dmkfasi/nus-cpu/kicad/cpu-rcp/PCB-3d-preview-bottom.png

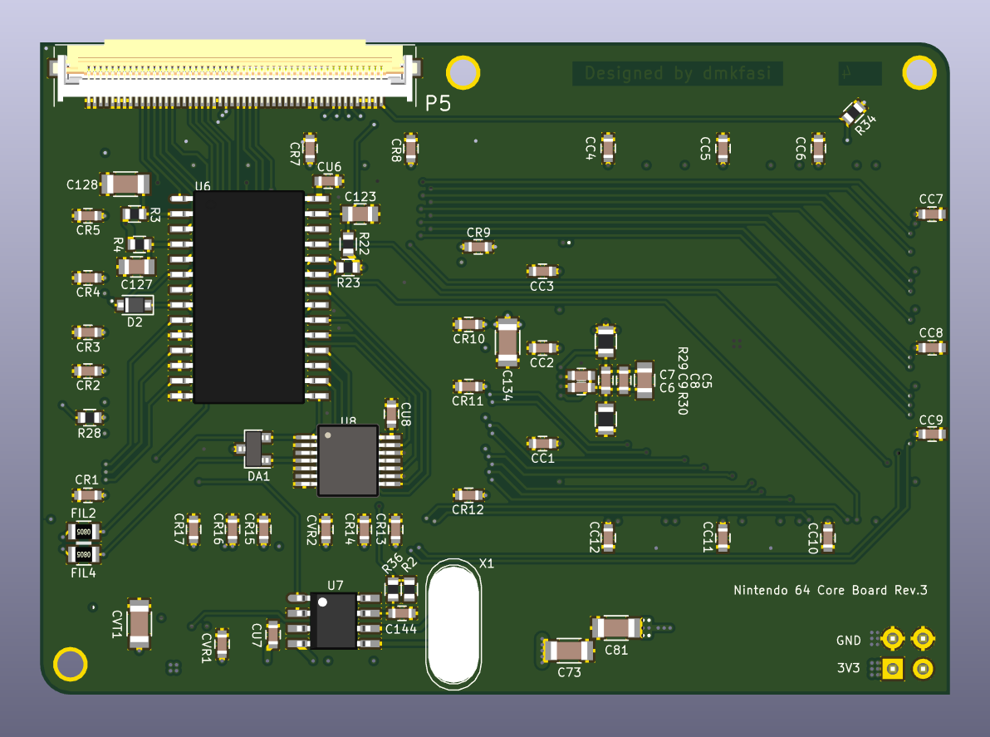
kicad/cpu-rcp/PCB-3d-preview-bottom.png
