dmkfasi/nus-cpu/kicad/cpu-rcp/PCB-3d-preview-top.png

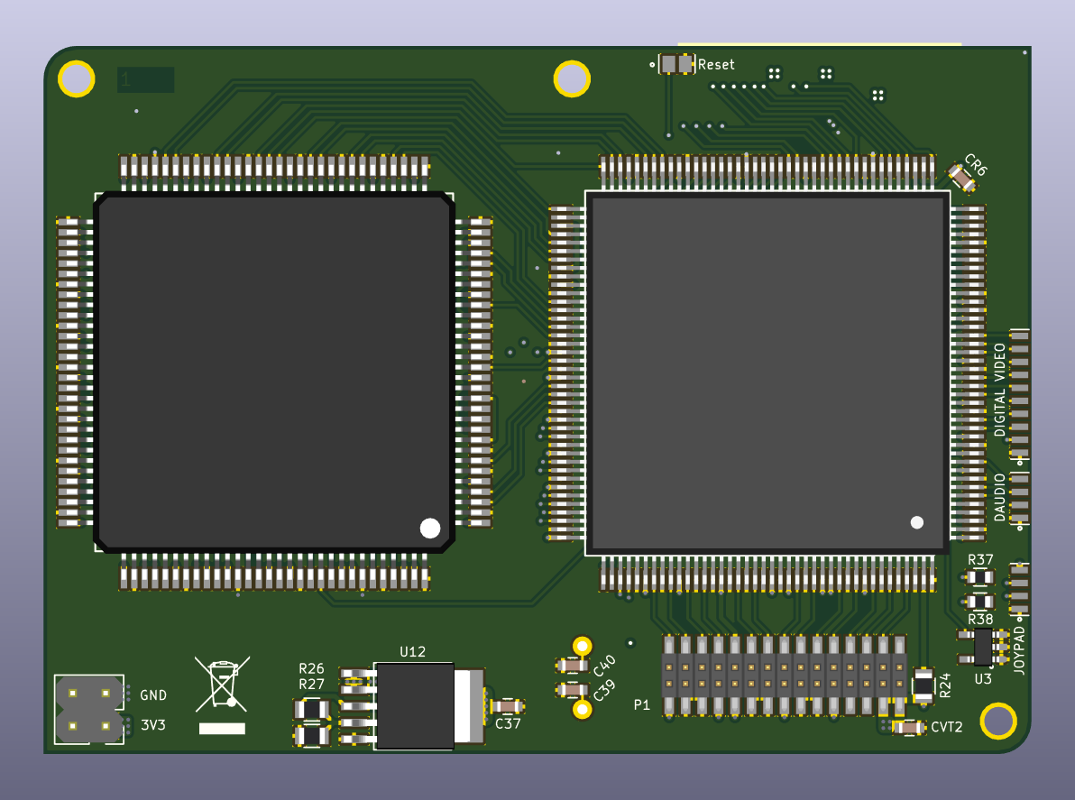
kicad/cpu-rcp/PCB-3d-preview-top.png
