dmkfasi/nus-cpu/kicad/rcp-cart/PCB-3d-preview-bottom.png

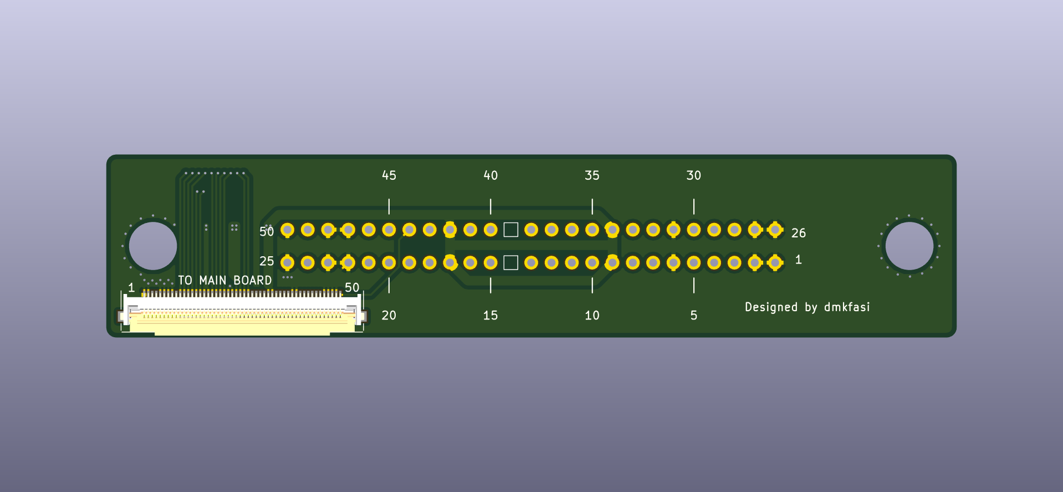
kicad/rcp-cart/PCB-3d-preview-bottom.png
