dmkfasi/nus-cpu/kicad/rcp-cart/PCB-3d-preview-top.png

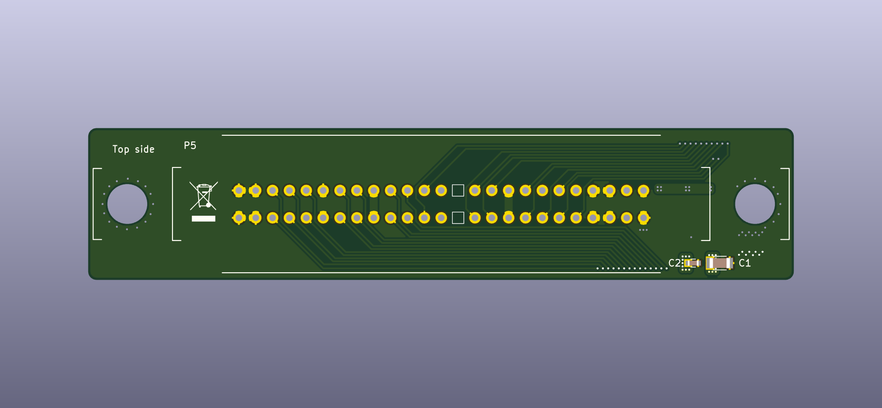
kicad/rcp-cart/PCB-3d-preview-top.png
