dmkfasi/nus-cpu/kicad/rcp-rdram/PCB-3d-preview-bottom.png

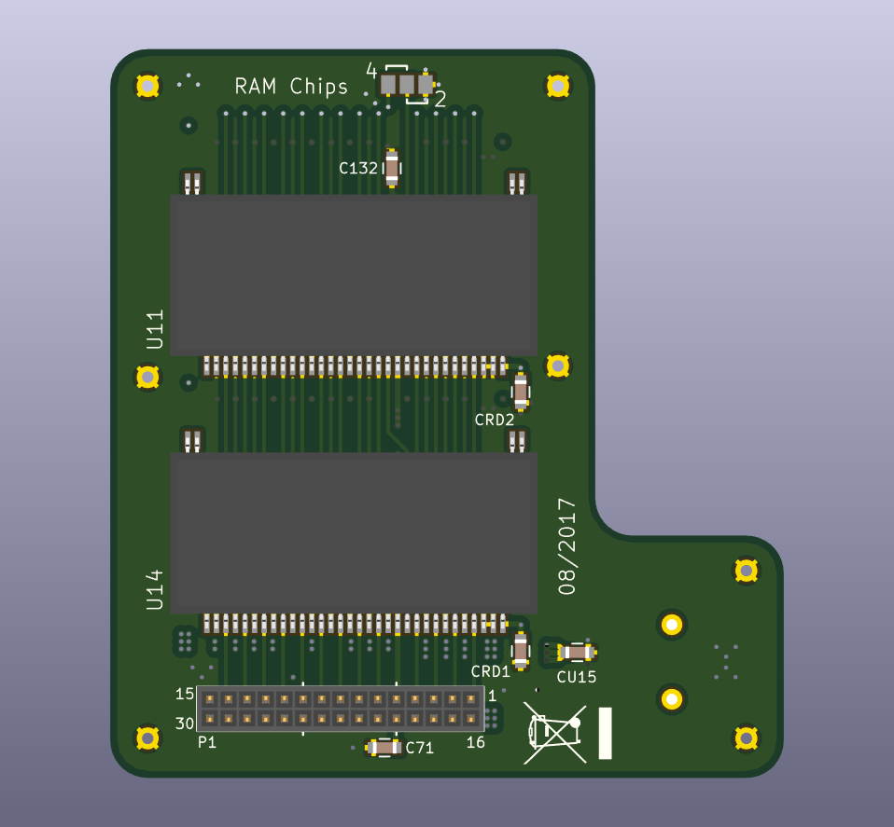
kicad/rcp-rdram/PCB-3d-preview-bottom.png
