dmkfasi/nus-cpu/kicad/rcp-rdram/PCB-3d-preview-top.png

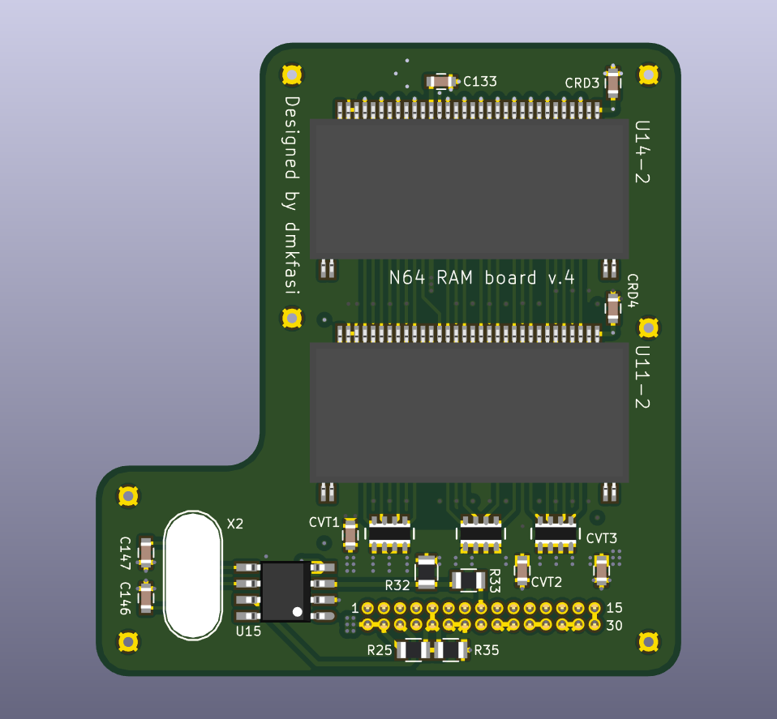
kicad/rcp-rdram/PCB-3d-preview-top.png
