dmkfasi/nus-cpu/reference/n64-marshallh/ra58b10cfc242443986.png

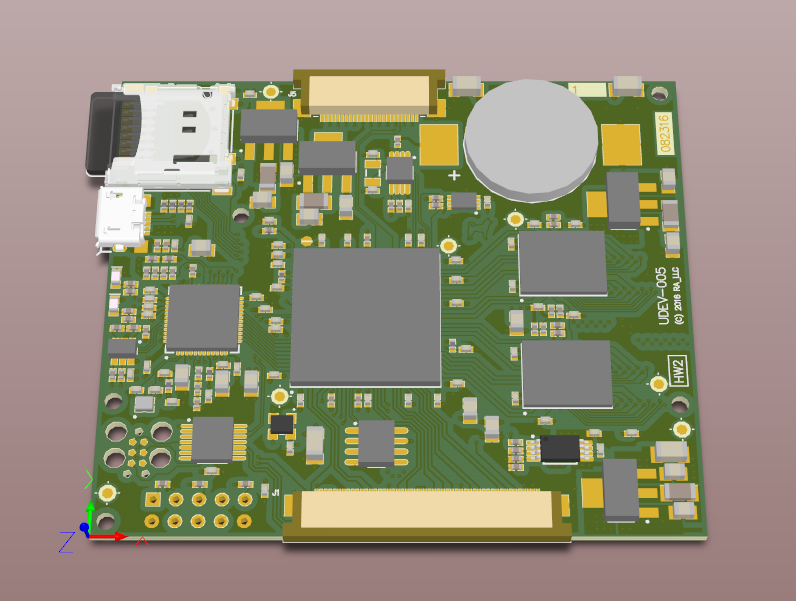
reference/n64-marshallh/ra58b10cfc242443986.png
