dmkfasi/nus-cpu/reference/n64-marshallh/ra58c47a2f7f03d1686.jpg

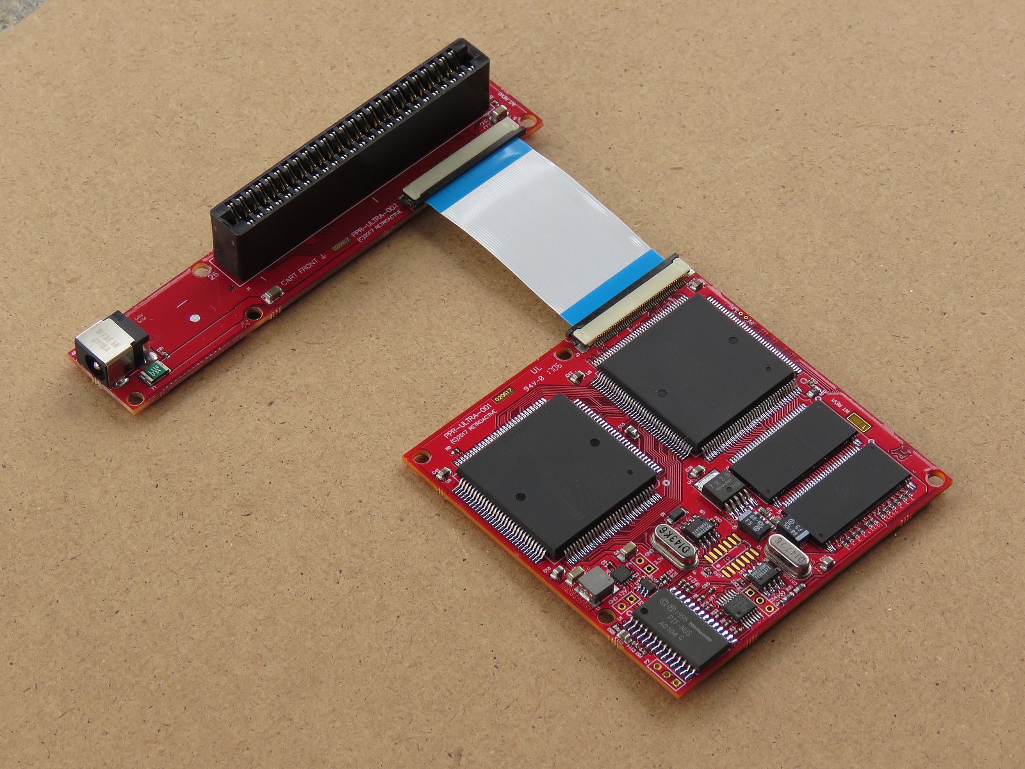
reference/n64-marshallh/ra58c47a2f7f03d1686.jpg
