dmkfasi/nus-cpu/reference/n64-marshallh/ra58c0643a46c8de22f.jpg

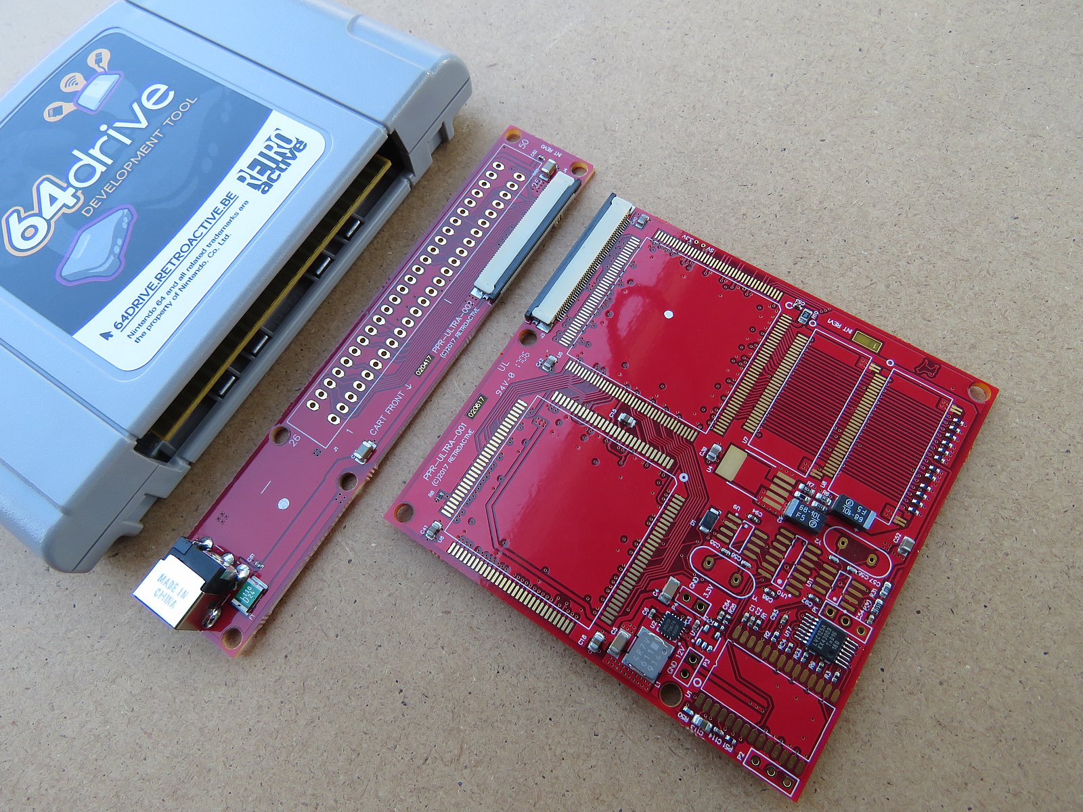
reference/n64-marshallh/ra58c0643a46c8de22f.jpg
