dmkfasi/nus-cpu/reference/n64-marshallh/ra58cd89858b0a0d140.jpg

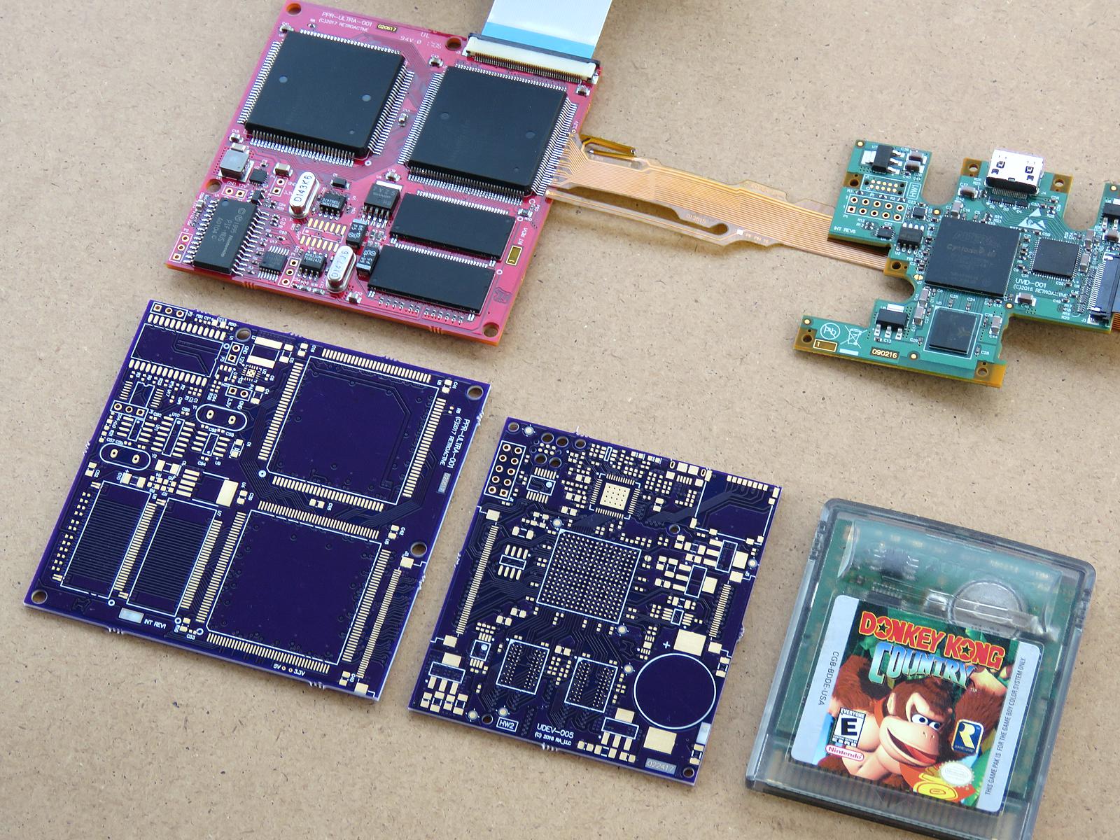
reference/n64-marshallh/ra58cd89858b0a0d140.jpg
