dmkfasi/nus-cpu/reference/n64-marshallh/ra58dc3f5d90e65ff34.jpg

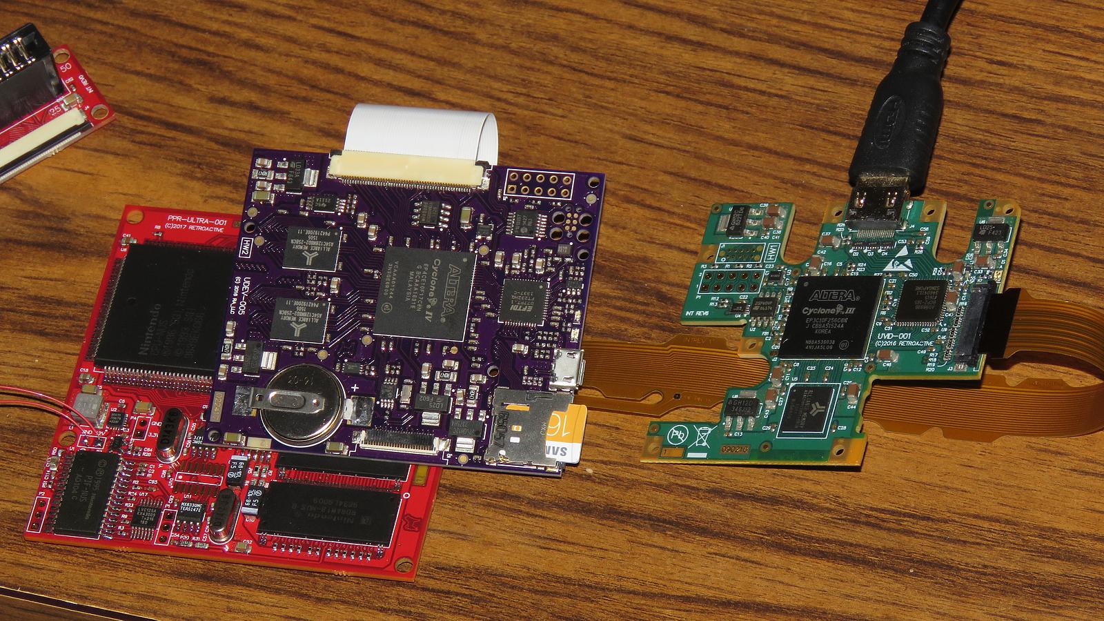
reference/n64-marshallh/ra58dc3f5d90e65ff34.jpg
