dmkfasi/nus-cpu/reference/n64-marshallh/ra58dc427e561e47eda.jpg

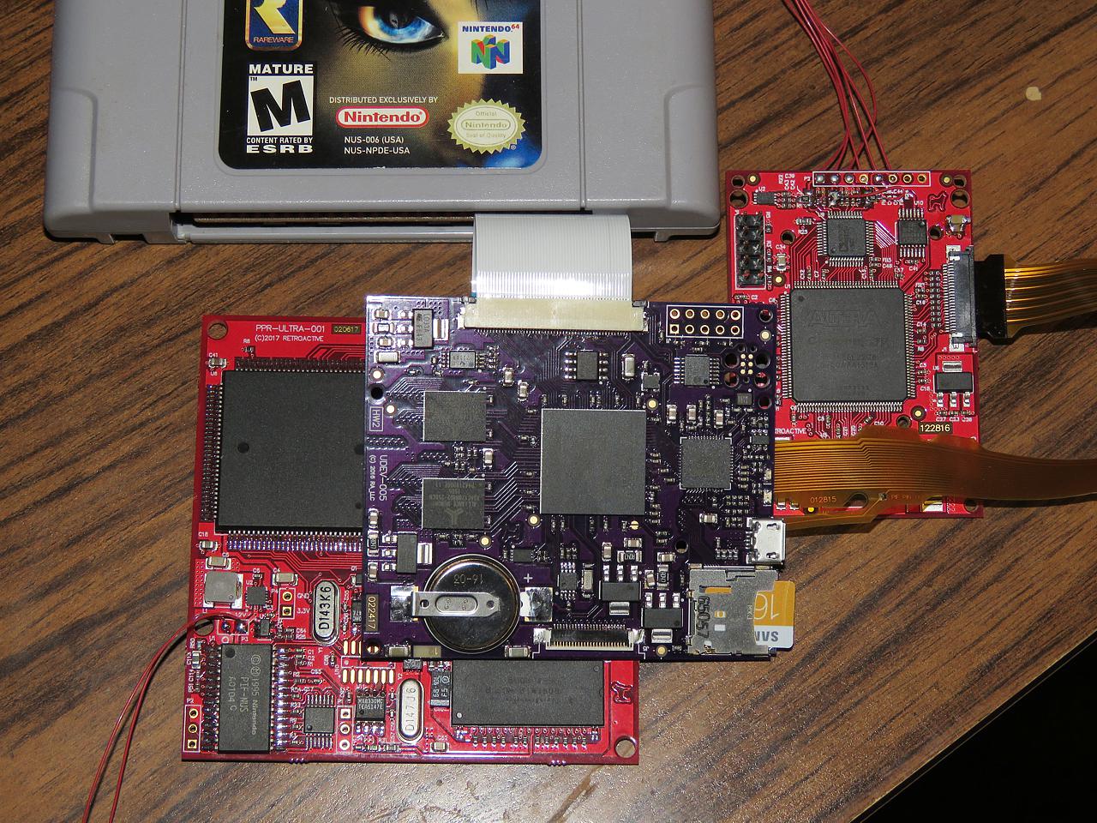
reference/n64-marshallh/ra58dc427e561e47eda.jpg
