dmkfasi/nus-cpu/reference/n64-marshallh/ra58dc394424cff16f6.jpg

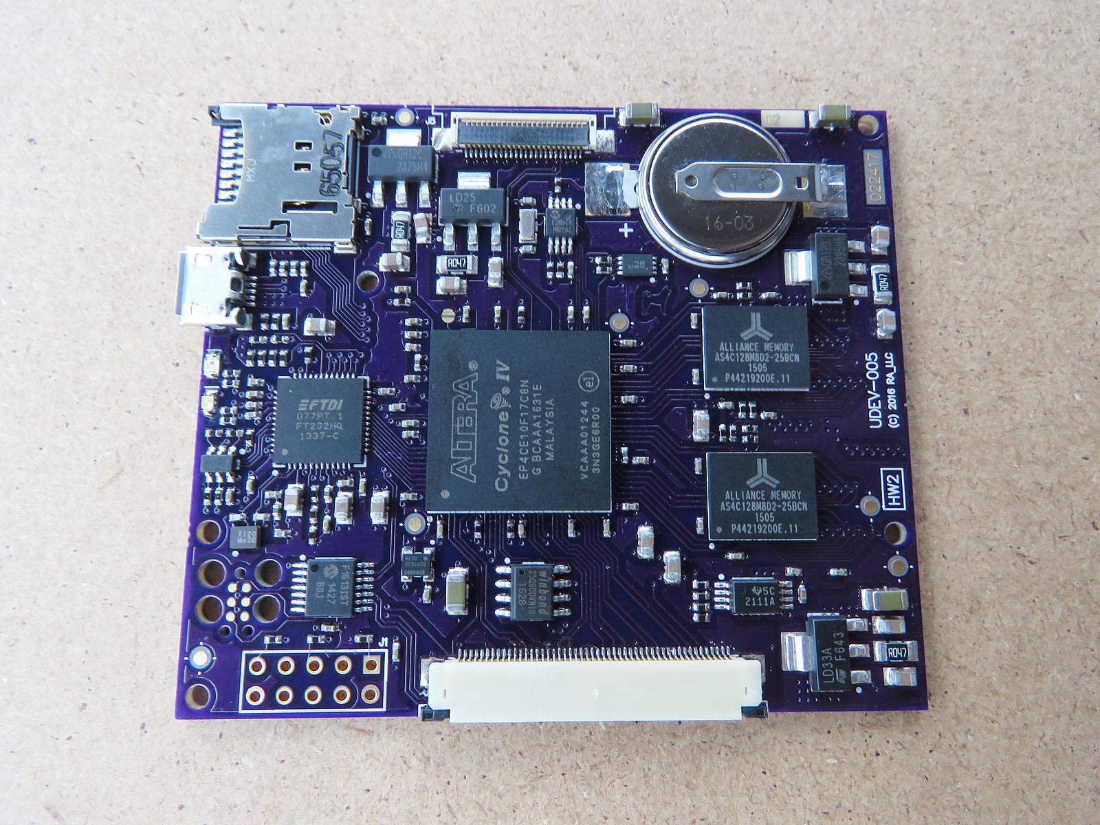
reference/n64-marshallh/ra58dc394424cff16f6.jpg
