dmkfasi/nus-cpu/reference/n64-marshallh/ra58fe89d2181fc5a18.png

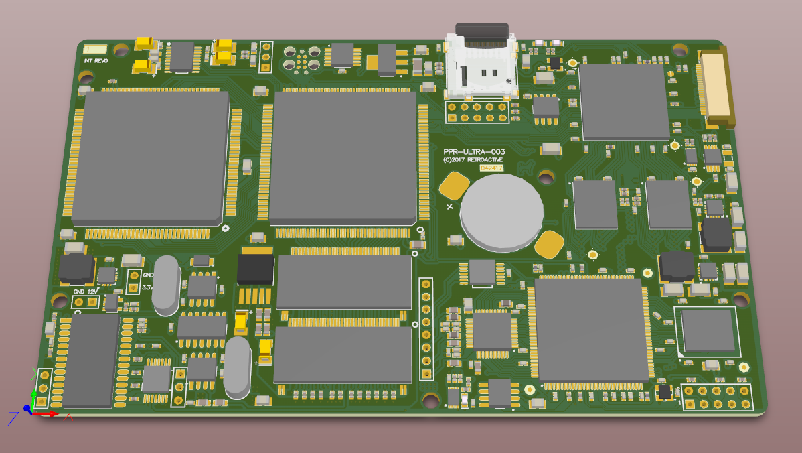
reference/n64-marshallh/ra58fe89d2181fc5a18.png
