dmkfasi/nus-cpu/reference/n64-marshallh/ra58fe877286c67c202.png

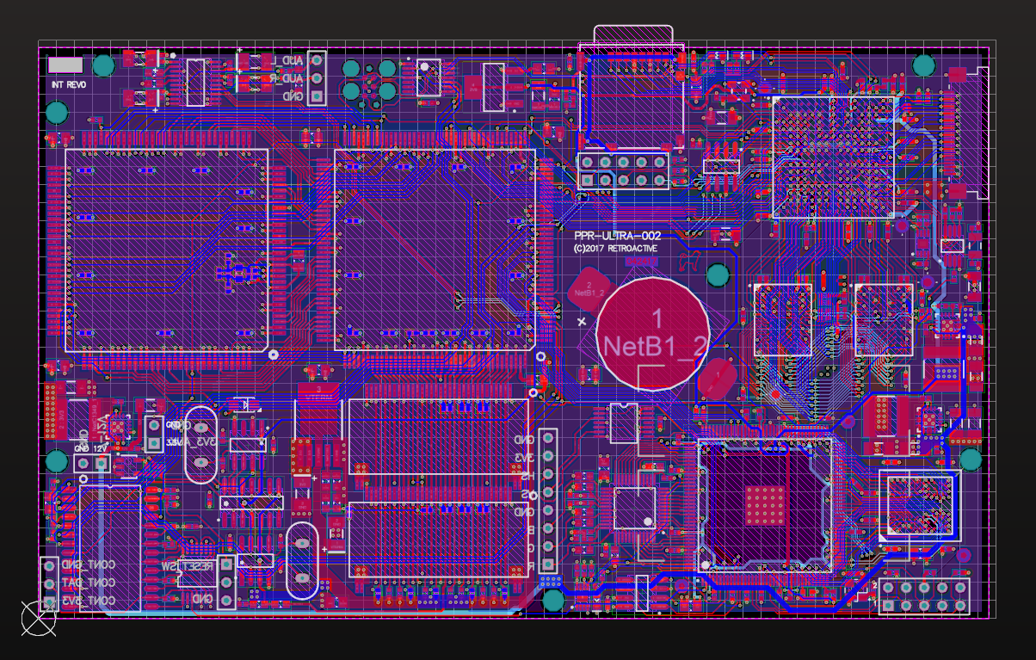
reference/n64-marshallh/ra58fe877286c67c202.png
