dmkfasi/nus-cpu/reference/n64-marshallh/ra588ce74976bb9afa8.jpg

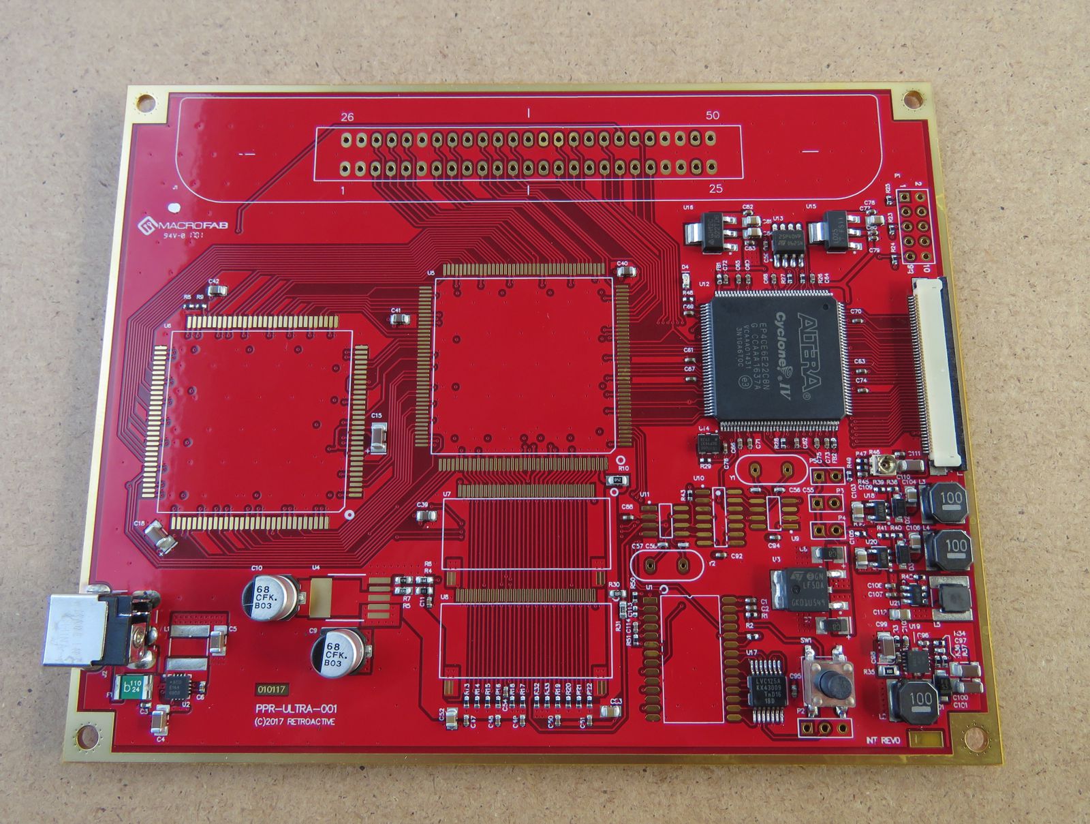
reference/n64-marshallh/ra588ce74976bb9afa8.jpg
