dmkfasi/nus-cpu/reference/n64-marshallh/ra588e489f1ec7b8442.jpg

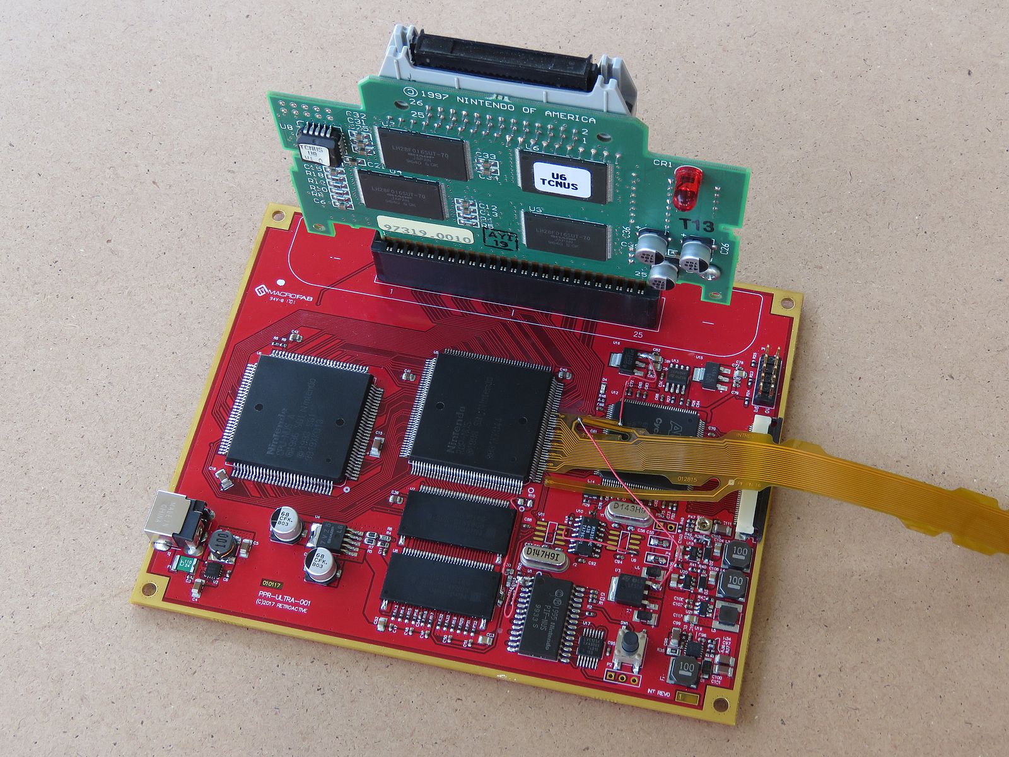
reference/n64-marshallh/ra588e489f1ec7b8442.jpg
