dmkfasi/nus-cpu/reference/n64-marshallh/ra5869ab79de0d7c09b.png

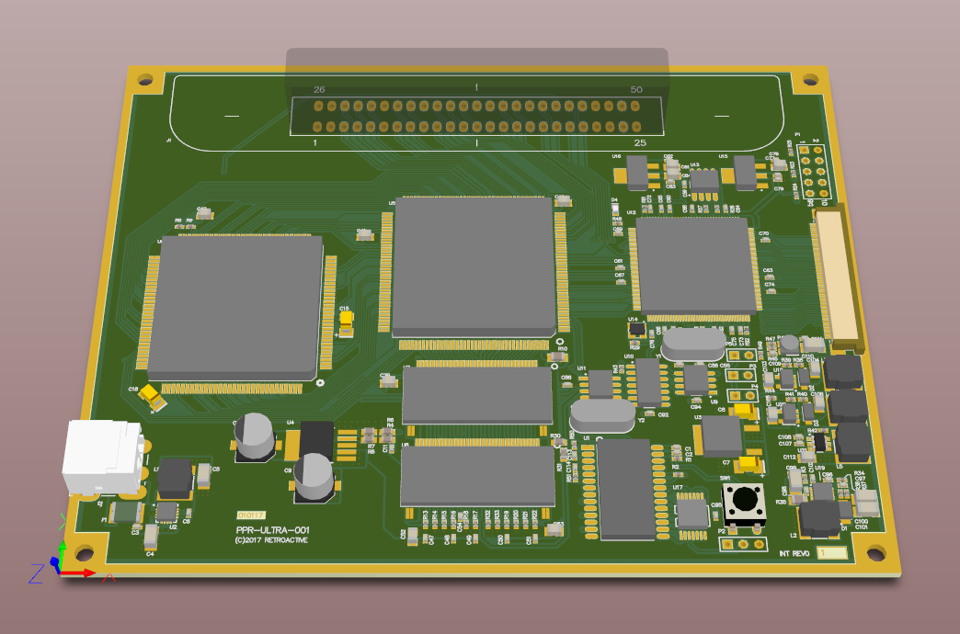
reference/n64-marshallh/ra5869ab79de0d7c09b.png
