dmkfasi/nus-cpu/reference/n64-marshallh/ra5869d1bb45a788b08.png

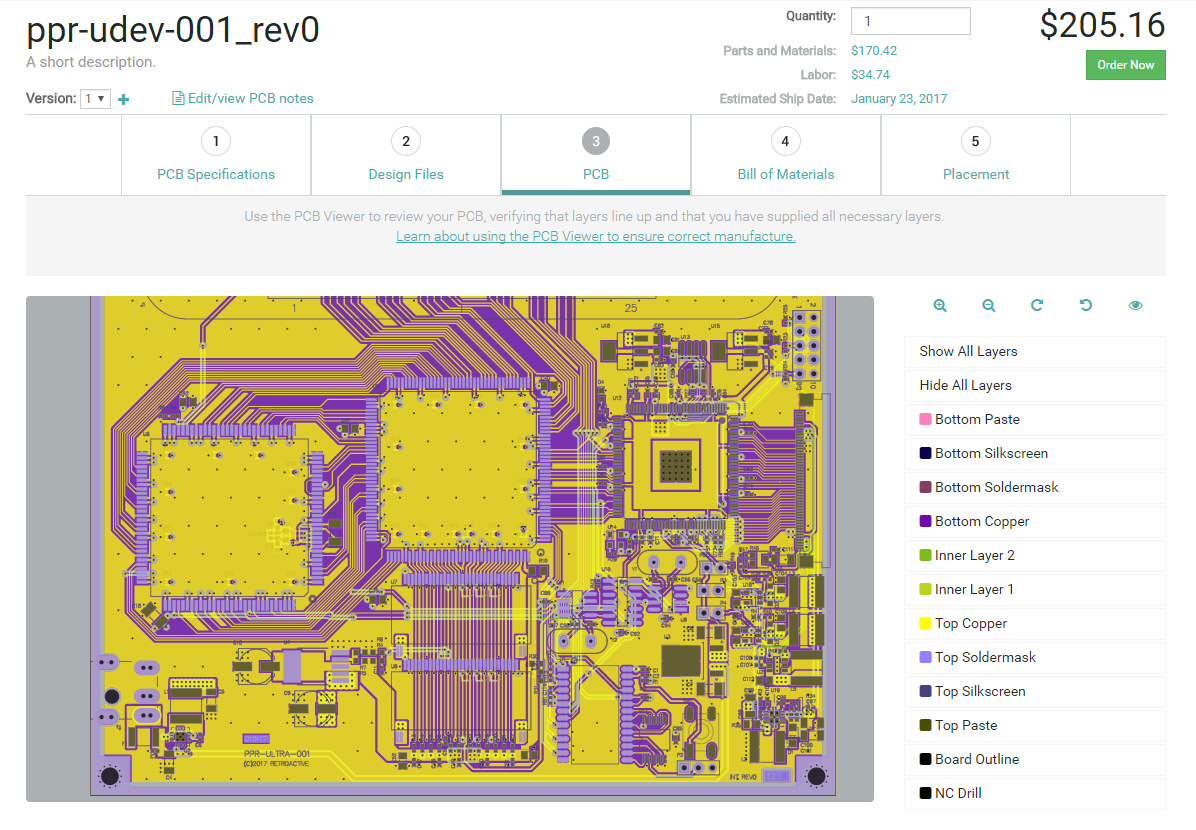
reference/n64-marshallh/ra5869d1bb45a788b08.png
