dmkfasi/nus-cpu/reference/n64-marshallh/ra5877c3ecaf056e521.png

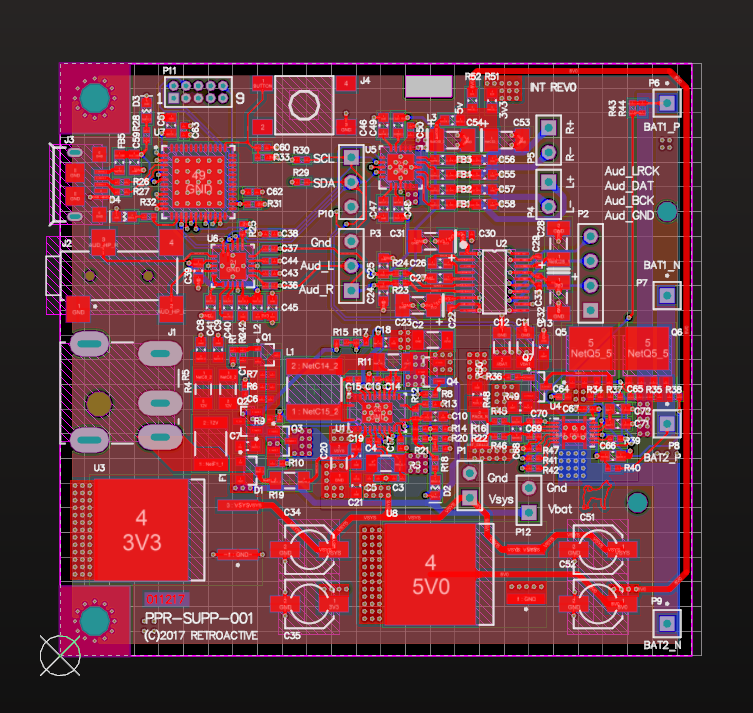
reference/n64-marshallh/ra5877c3ecaf056e521.png
