dmkfasi/nus-cpu/reference/n64-marshallh/ra5877c6db6ab1510e0.png

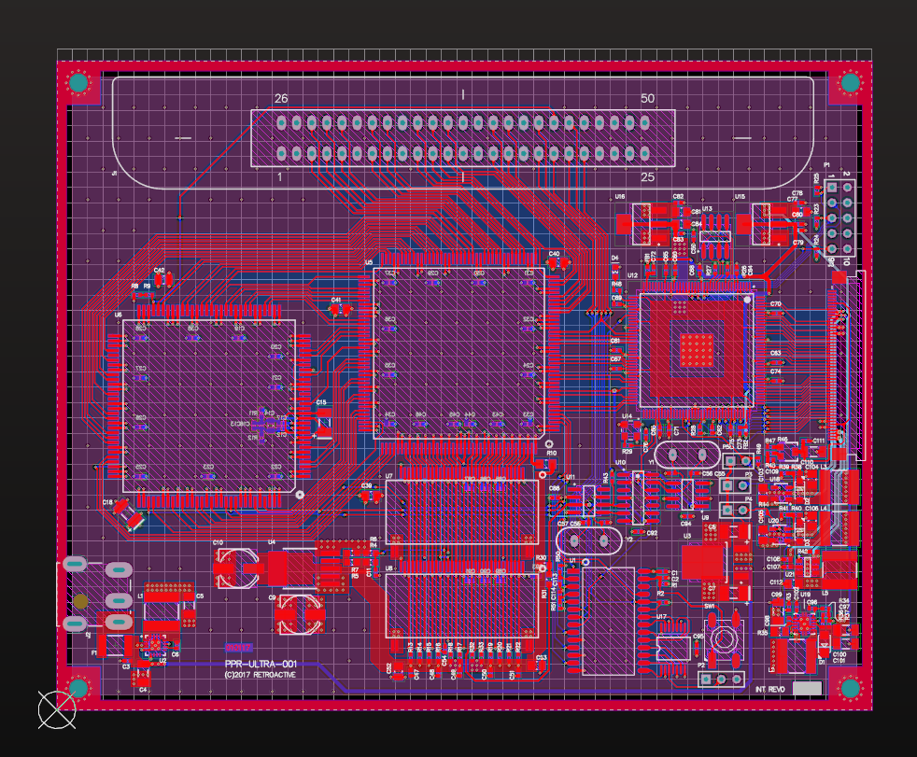
reference/n64-marshallh/ra5877c6db6ab1510e0.png
