dmkfasi/nus-cpu/reference/n64-marshallh/ra5925fa05948f99520.jpg

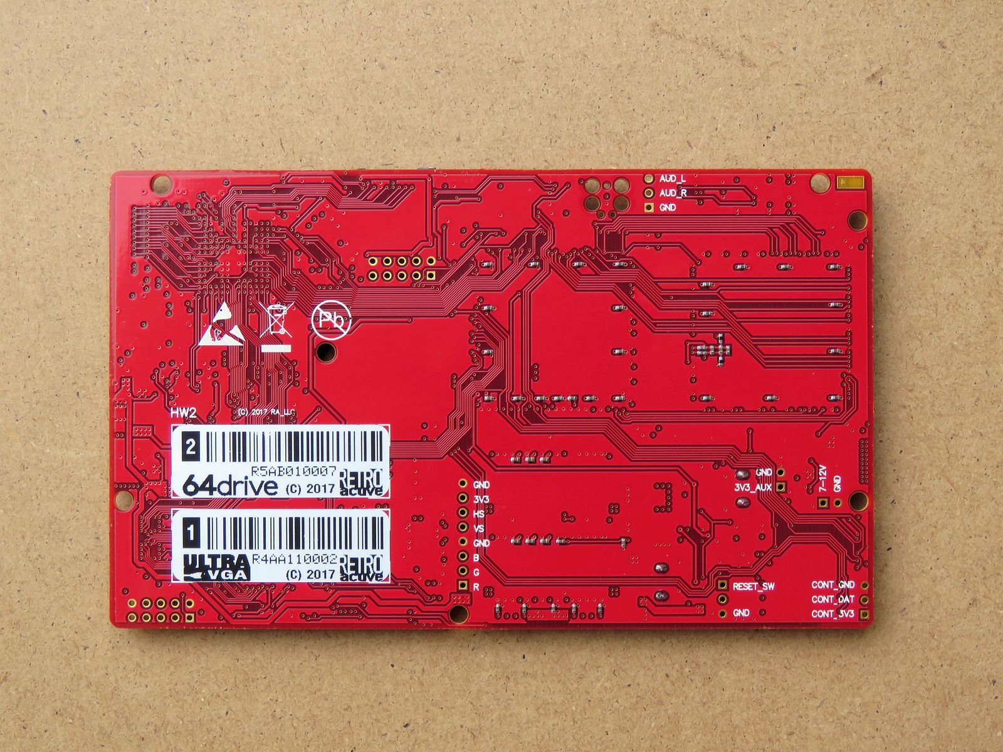
reference/n64-marshallh/ra5925fa05948f99520.jpg
