dmkfasi/nus-cpu/reference/n64-marshallh/ra5925fc53f3825d982.jpg

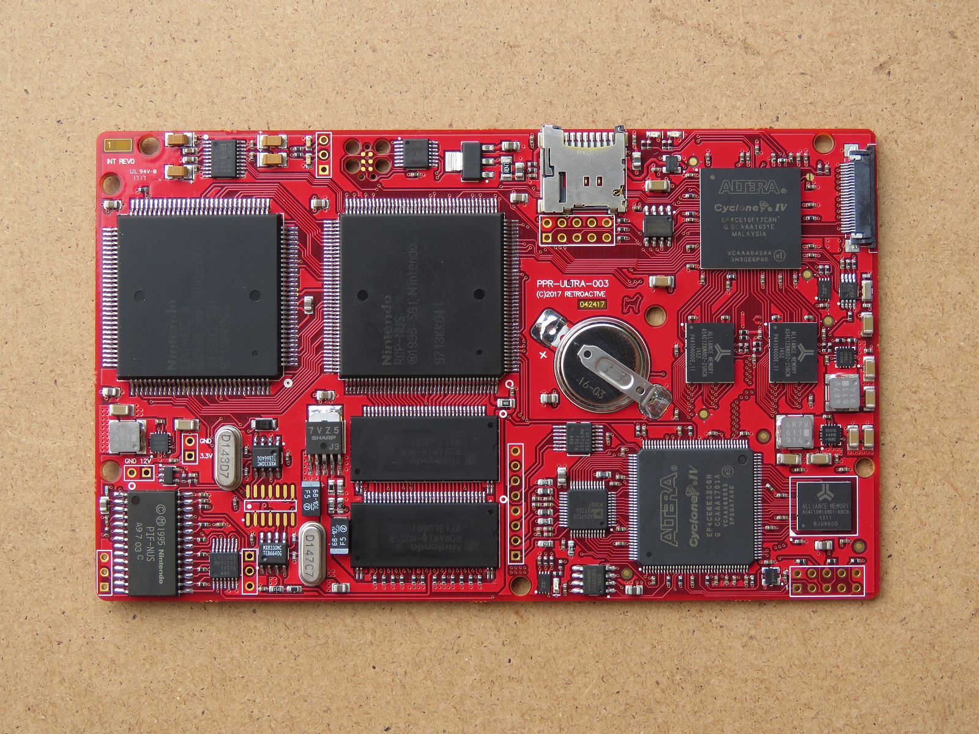
reference/n64-marshallh/ra5925fc53f3825d982.jpg
