dmkfasi/nus-cpu/reference/n64-marshallh/ra5959c7e0f3a951d8c.jpg

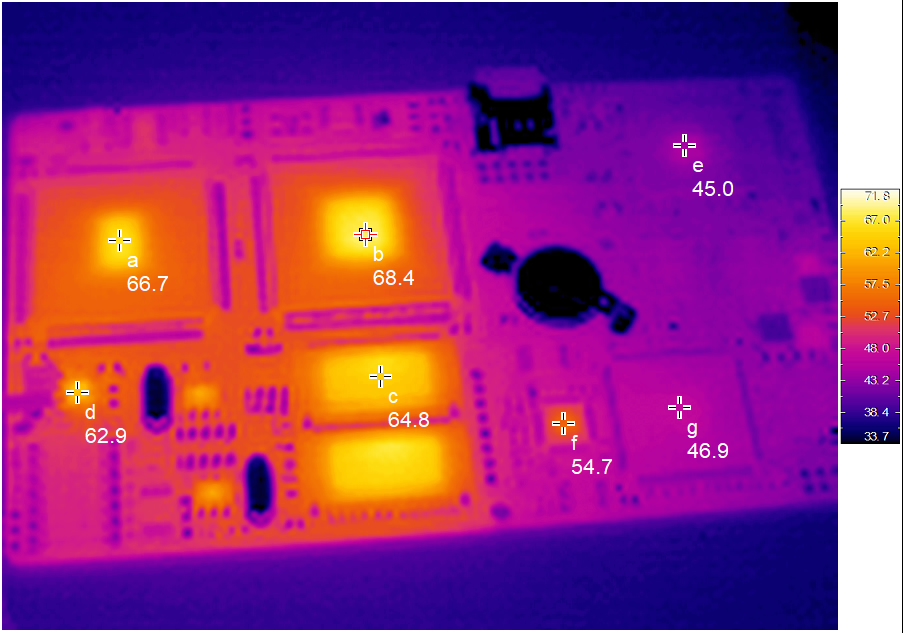
reference/n64-marshallh/ra5959c7e0f3a951d8c.jpg
