dmkfasi/nus-cpu/reference/n64-marshallh/ra58771da7159c2eef9.png

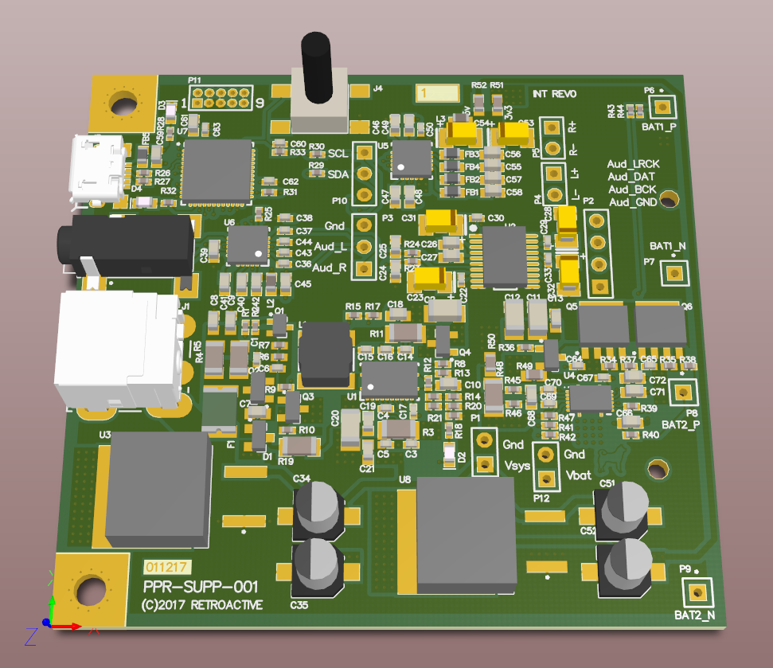
reference/n64-marshallh/ra58771da7159c2eef9.png
