dmkfasi/nus-cpu/reference/n64-marshallh/ra58929f7f12cb957d5.jpg

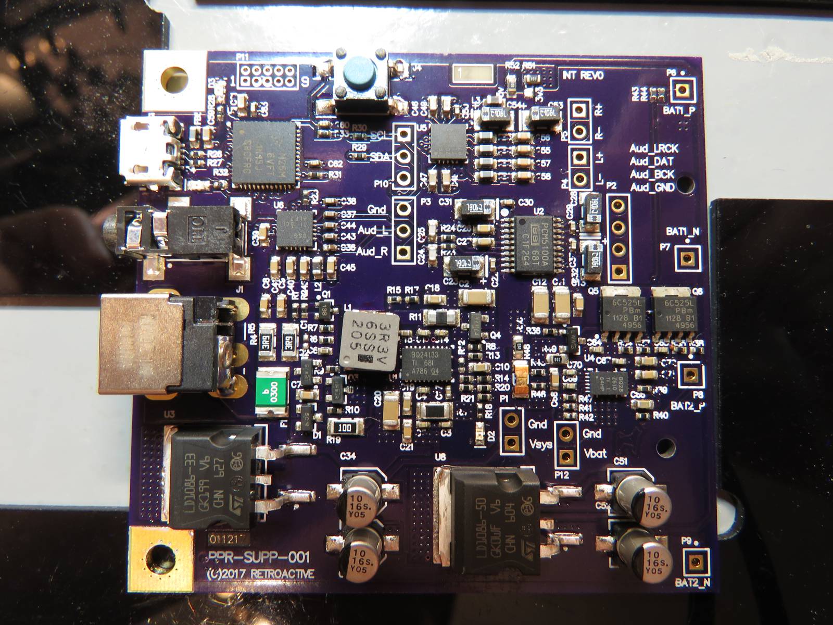
reference/n64-marshallh/ra58929f7f12cb957d5.jpg
