dmkfasi/nus-cpu/reference/n64-marshallh/ra59654d515e9111a43.jpg

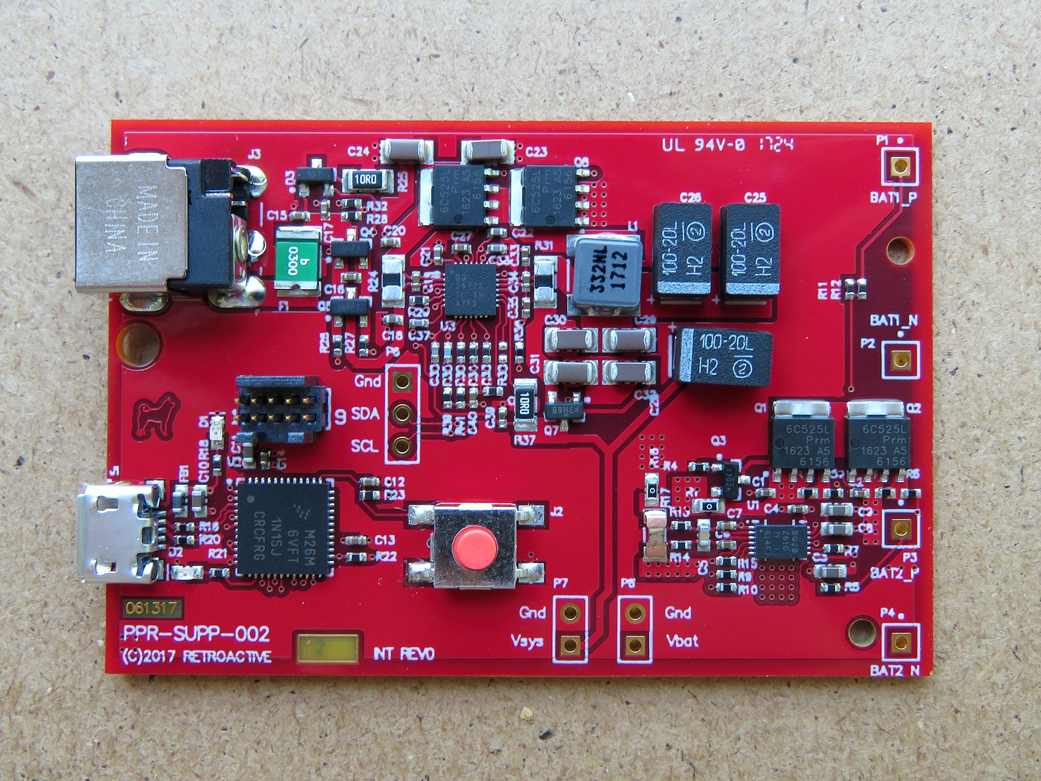
reference/n64-marshallh/ra59654d515e9111a43.jpg
