dmkfasi/nus-cpu/reference/n64-marshallh/ra586701c5acb63817e.png

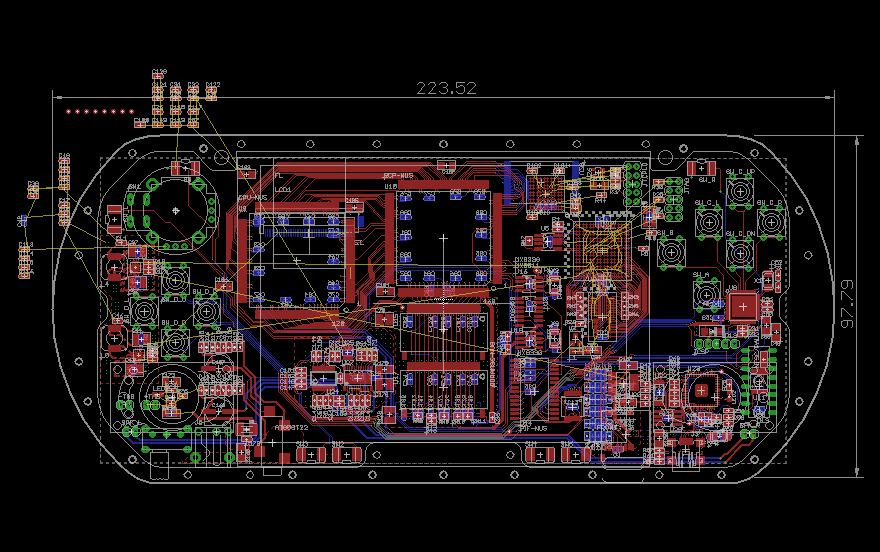
reference/n64-marshallh/ra586701c5acb63817e.png
