dmkfasi/nus-cpu/reference/n64-marshallh/ra586845e5d66768dc4.png

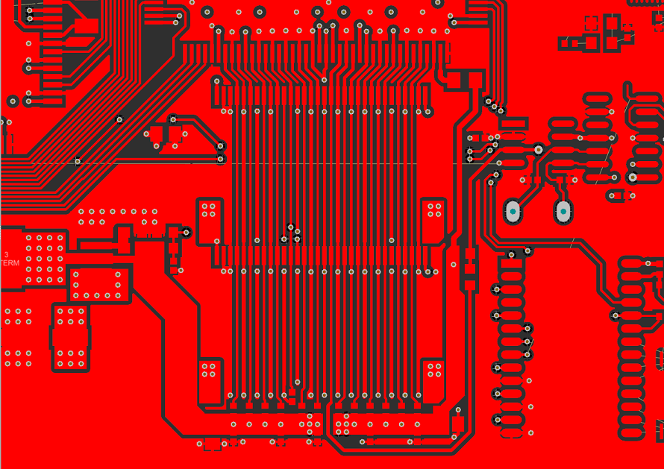
reference/n64-marshallh/ra586845e5d66768dc4.png
