dmkfasi/nus-cpu/reference/n64-marshallh/ra5886822dd67f325fe.jpg

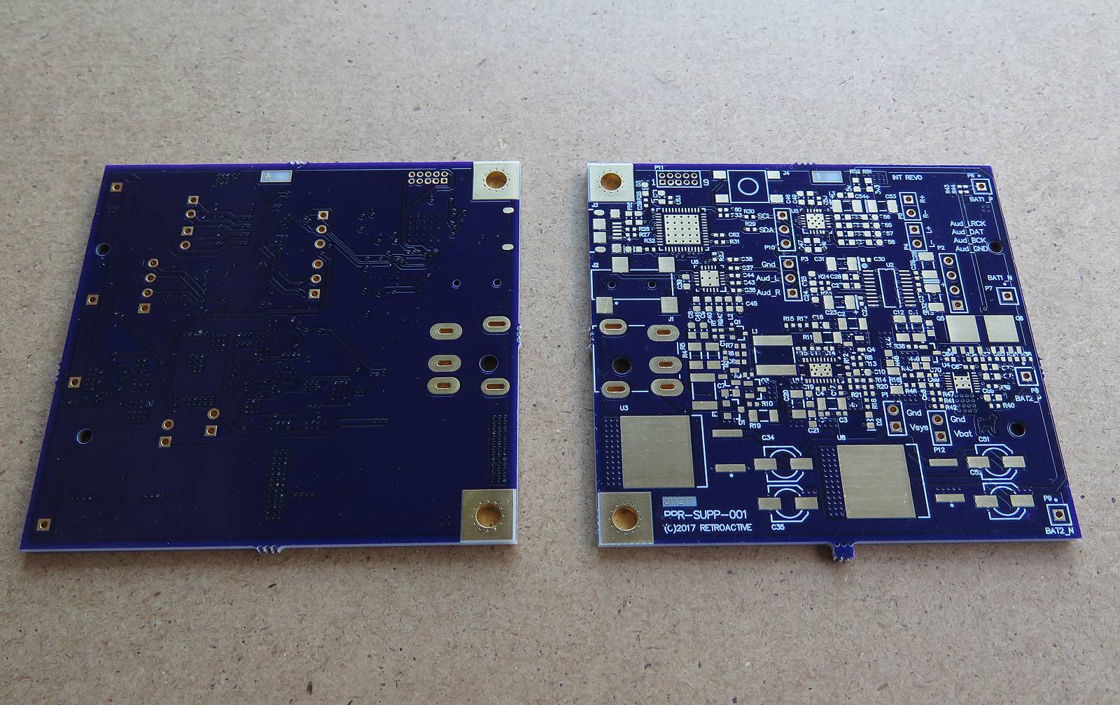
reference/n64-marshallh/ra5886822dd67f325fe.jpg
