dmkfasi/nus-cpu/reference/n64-marshallh/ra5895073aca5e7a58e.png

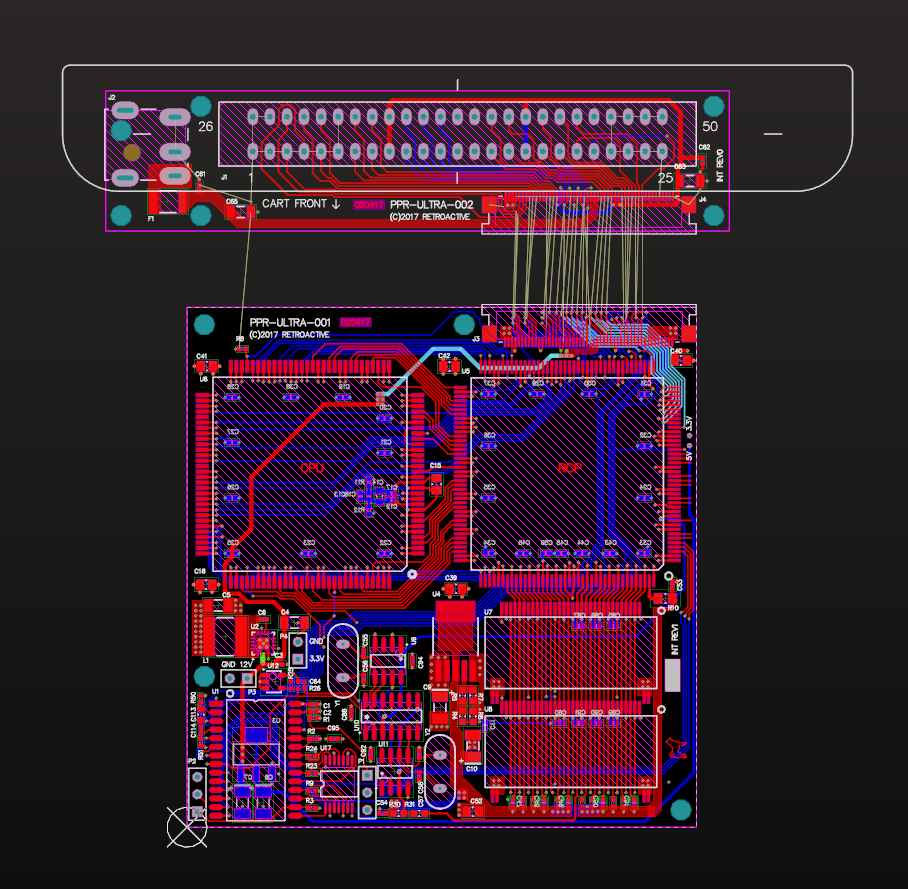
reference/n64-marshallh/ra5895073aca5e7a58e.png
