dmkfasi/nus-cpu/reference/NUS-Scans/NUS-004_1.jpg

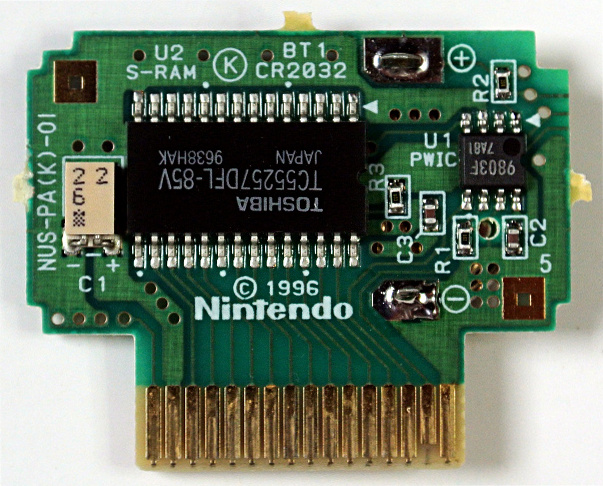
reference/NUS-Scans/NUS-004_1.jpg
