dmkfasi/nus-cpu/reference/NUS-Scans/NUS-004_2.jpg

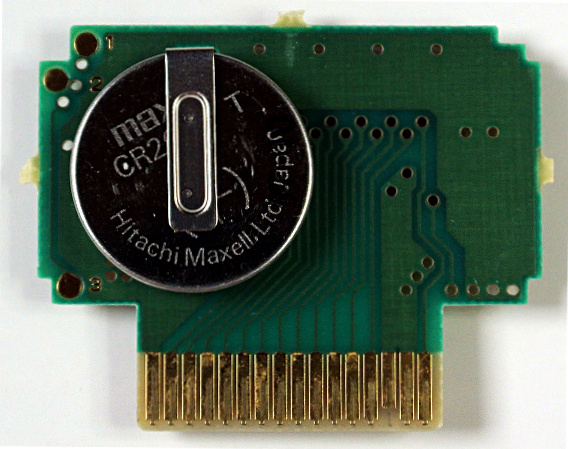
reference/NUS-Scans/NUS-004_2.jpg
