dmkfasi/nus-cpu/reference/NUS-Scans/NUS-005_1.jpg

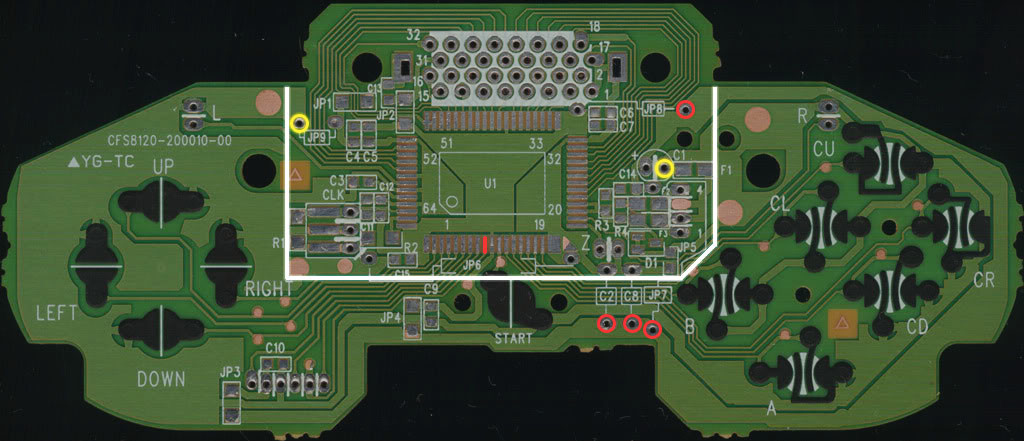
reference/NUS-Scans/NUS-005_1.jpg
