dmkfasi/nus-cpu/reference/NUS-Scans/NUS-007_1.jpg

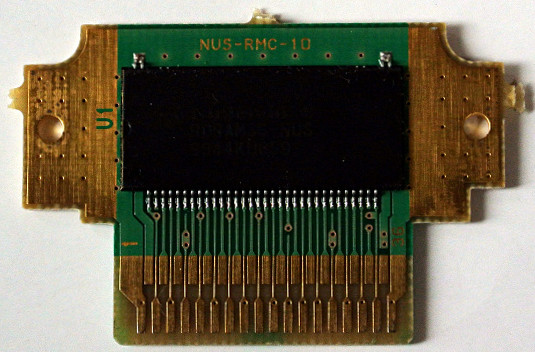
reference/NUS-Scans/NUS-007_1.jpg
