dmkfasi/nus-cpu/reference/NUS-Scans/NUS-007_2.jpg

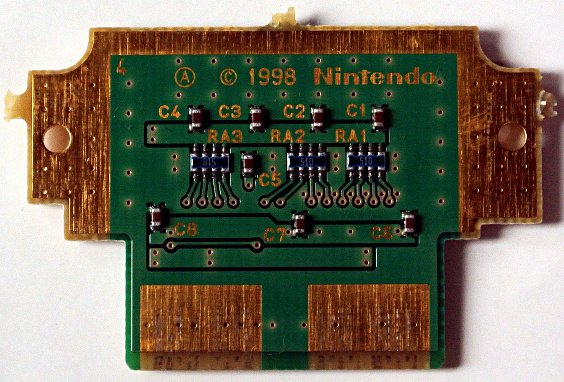
reference/NUS-Scans/NUS-007_2.jpg
