dmkfasi/nus-cpu/reference/NUS-Scans/NUS-008_1.jpg

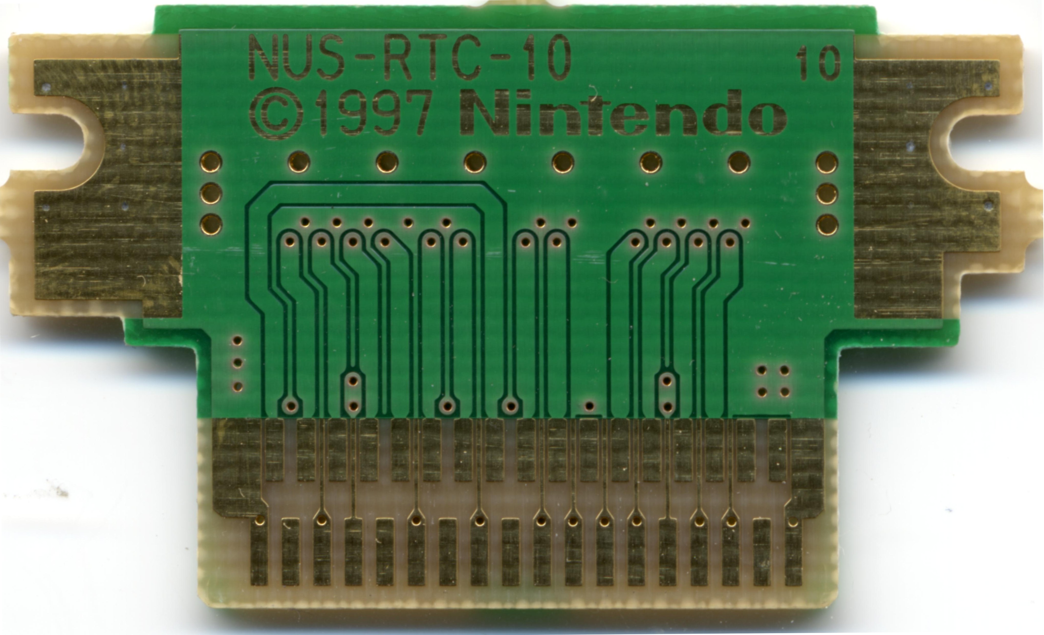
reference/NUS-Scans/NUS-008_1.jpg
