dmkfasi/nus-cpu/reference/NUS-Scans/NUS-008_2.jpg

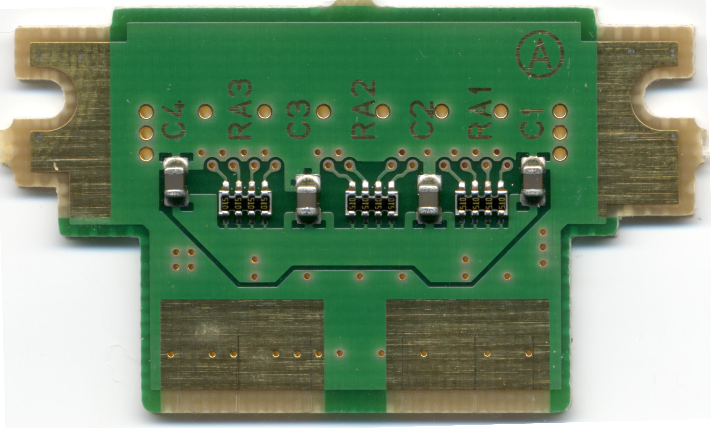
reference/NUS-Scans/NUS-008_2.jpg
