dmkfasi/nus-cpu/reference/NUS-Scans/NUS-CPU-04_1-CLEAN.jpg

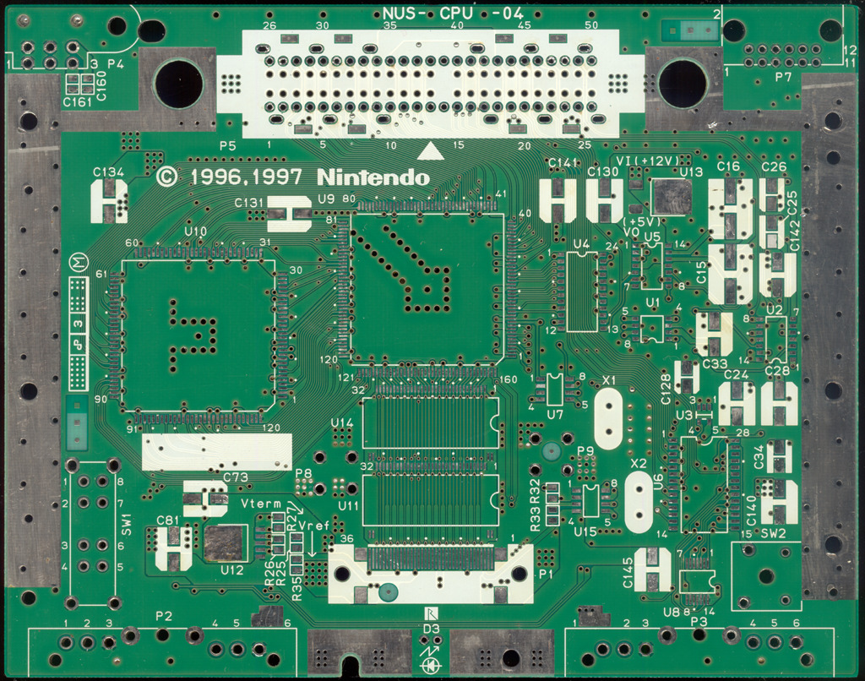
reference/NUS-Scans/NUS-CPU-04_1-CLEAN.jpg
