dmkfasi/nus-cpu/reference/NUS-Scans/NUS-CPU-04_01.jpg

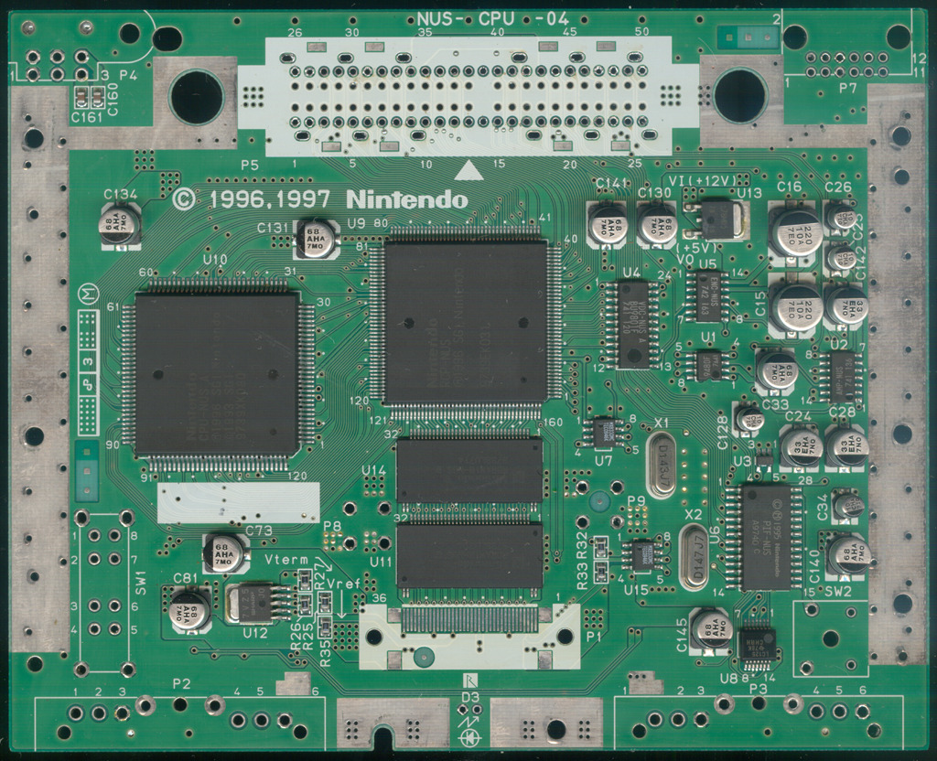
reference/NUS-Scans/NUS-CPU-04_01.jpg
