dmkfasi/nus-cpu/reference/NUS-Scans/NUS-CPU-04_2.jpg

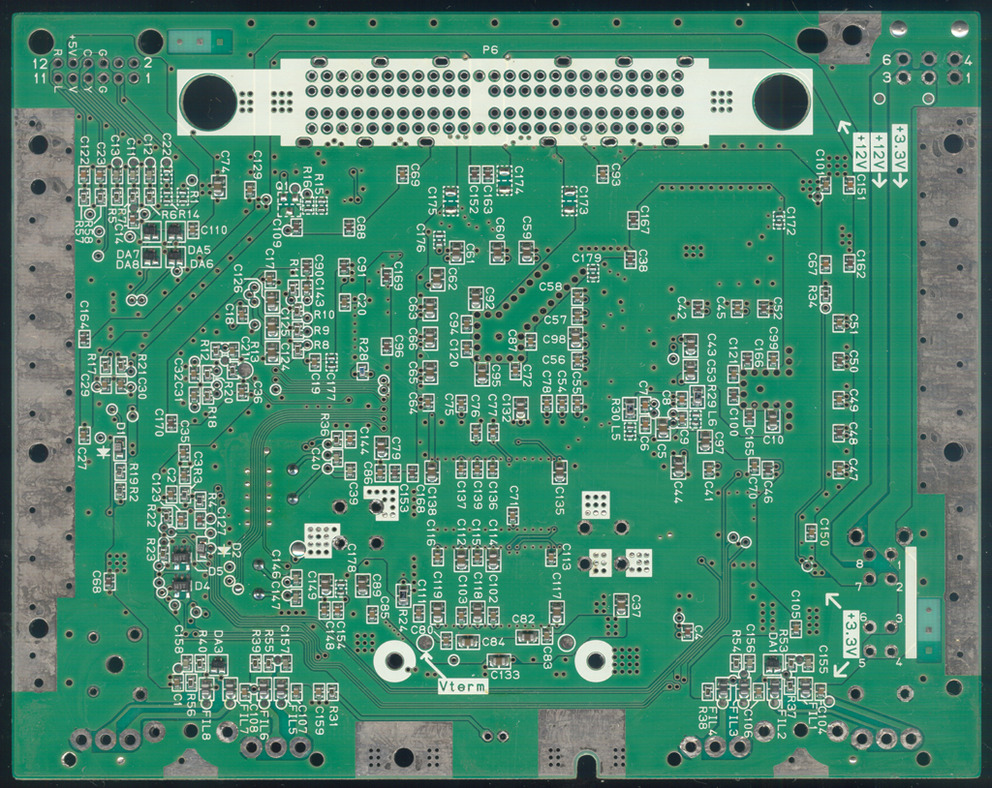
reference/NUS-Scans/NUS-CPU-04_2.jpg
