dmkfasi/nus-cpu/reference/NUS-Scans/NUS-CPU-08_1.BARECOPPER.jpg

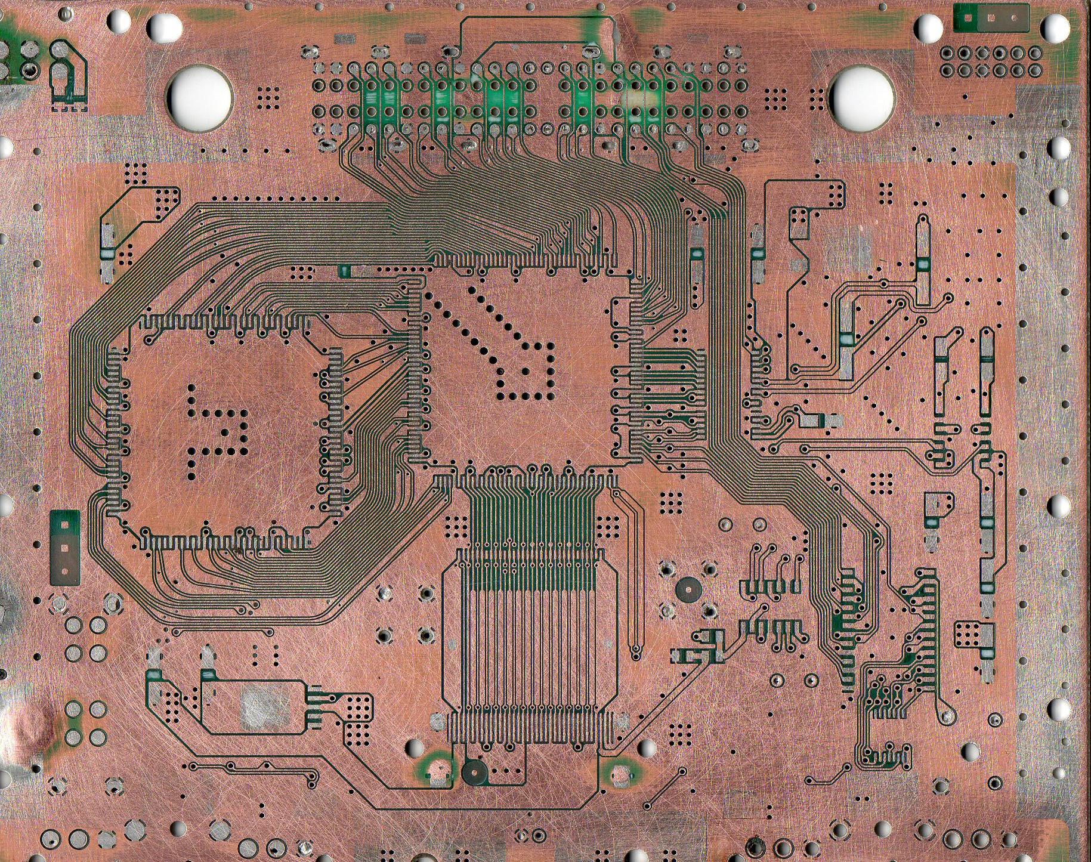
reference/NUS-Scans/NUS-CPU-08_1.BARECOPPER.jpg
