dmkfasi/nus-cpu/reference/PCB-Designs/1.png

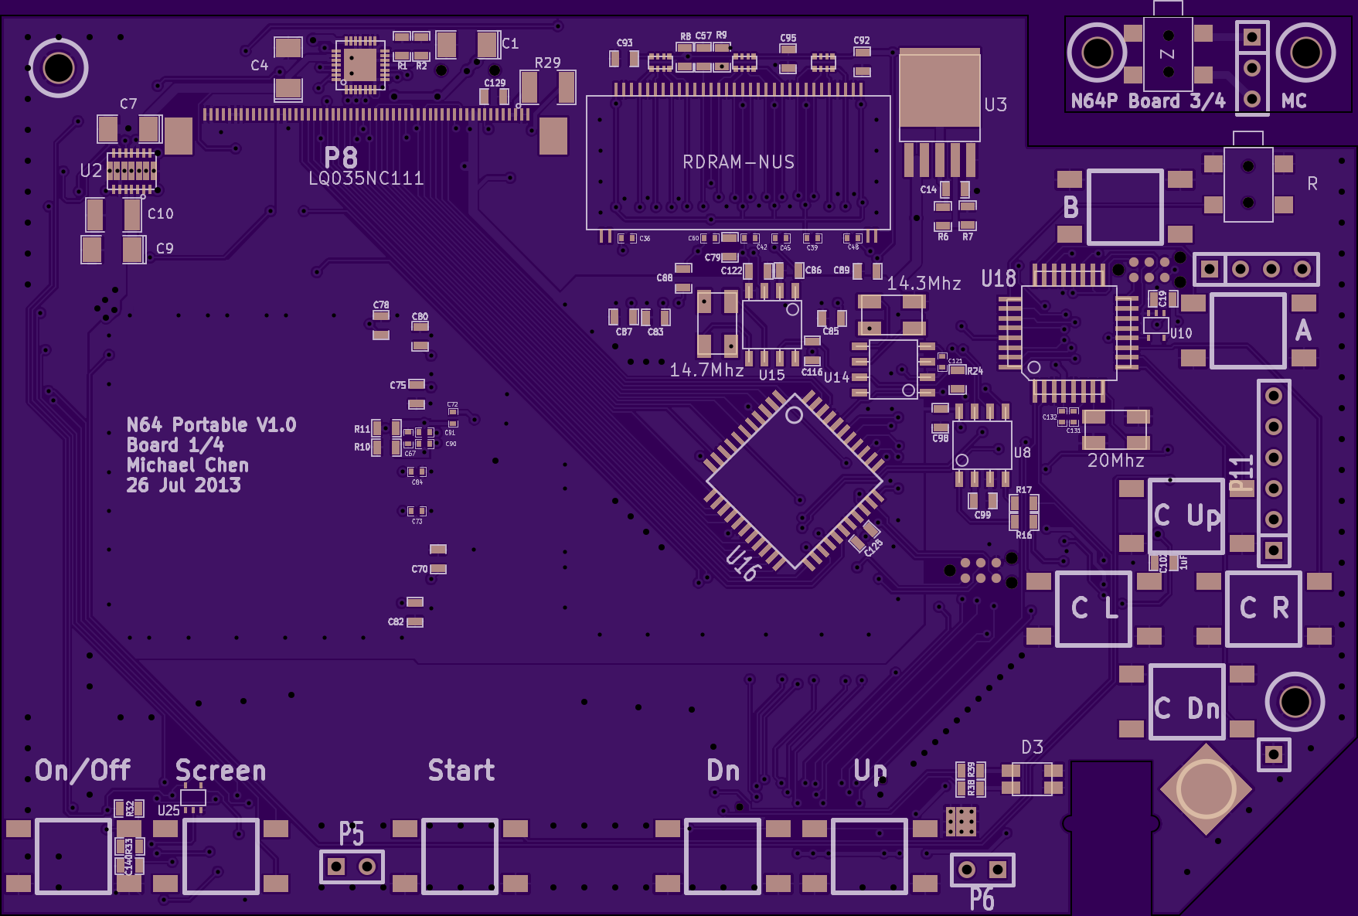
reference/PCB-Designs/1.png
