dmkfasi/nus-cpu/reference/PCB-Designs/2.png

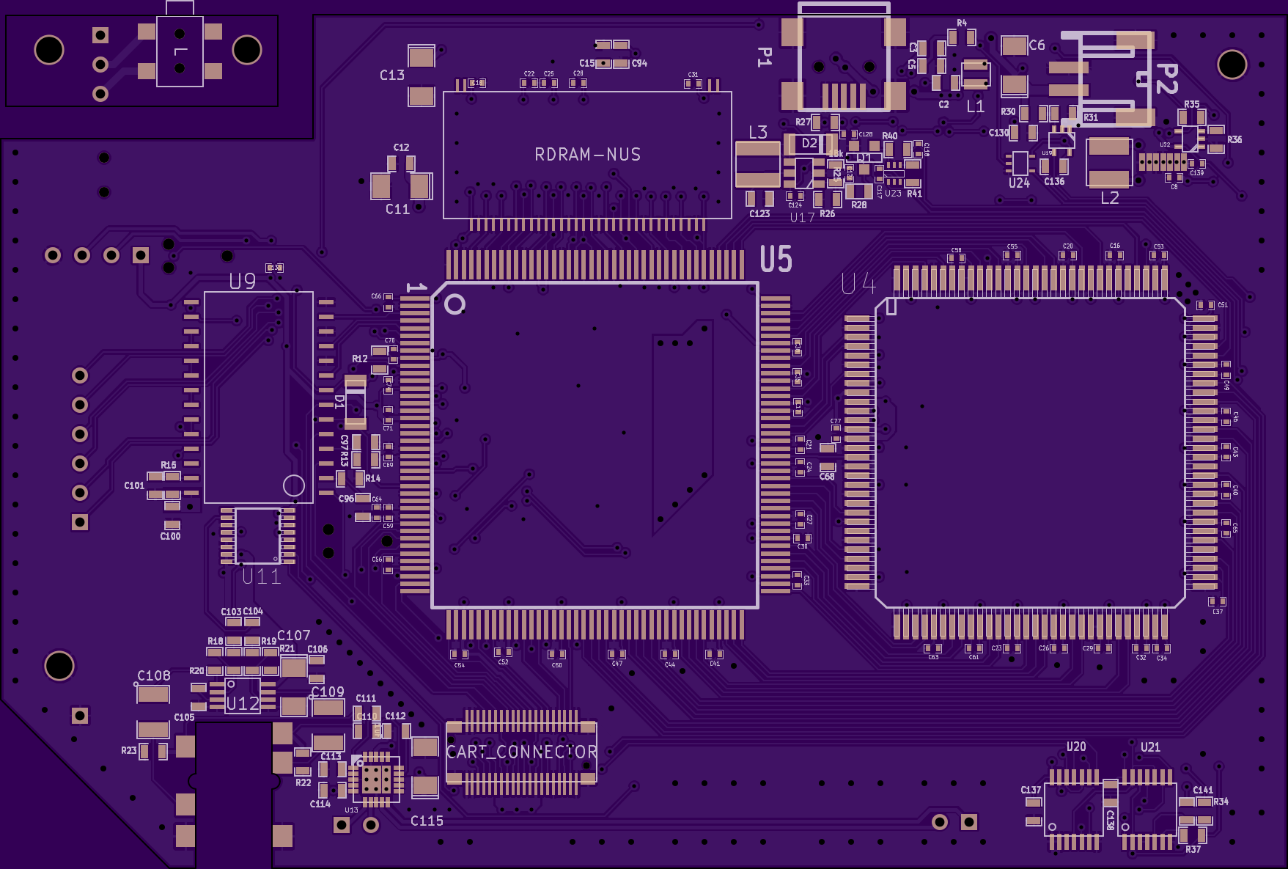
reference/PCB-Designs/2.png
