dmkfasi/nus-cpu/reference/PCB-Designs/3.png

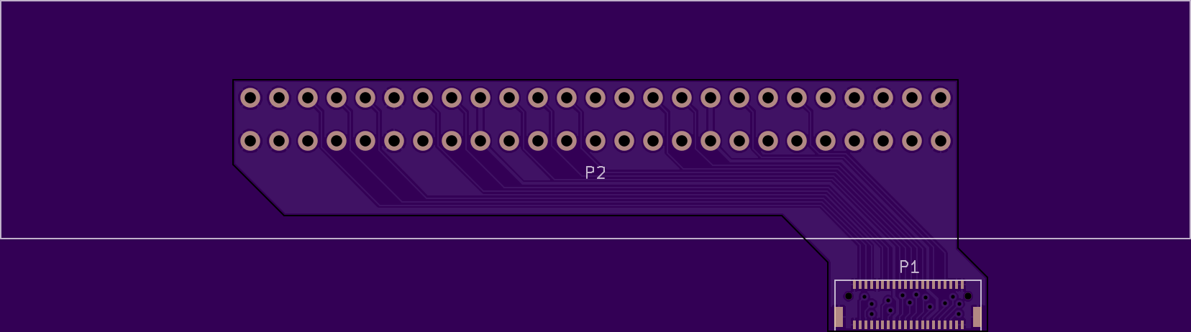
reference/PCB-Designs/3.png
