dmkfasi/nus-cpu/reference/PCB-Designs/4.png

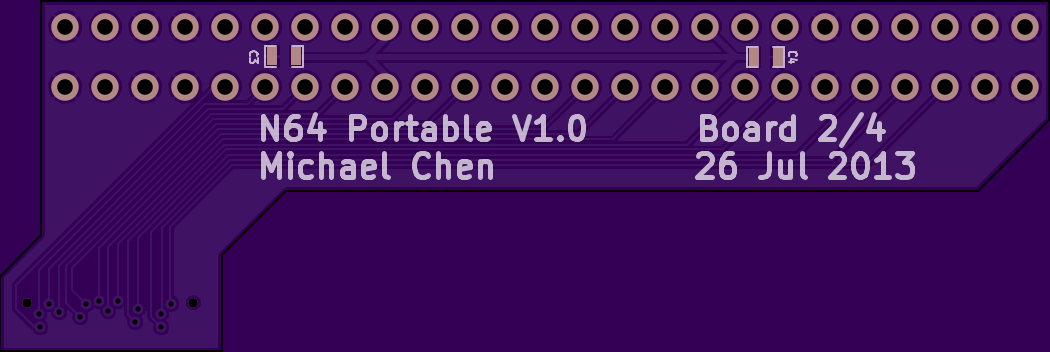
reference/PCB-Designs/4.png
