dmkfasi/nus-cpu/reference/PCB-Designs/layout.jpg

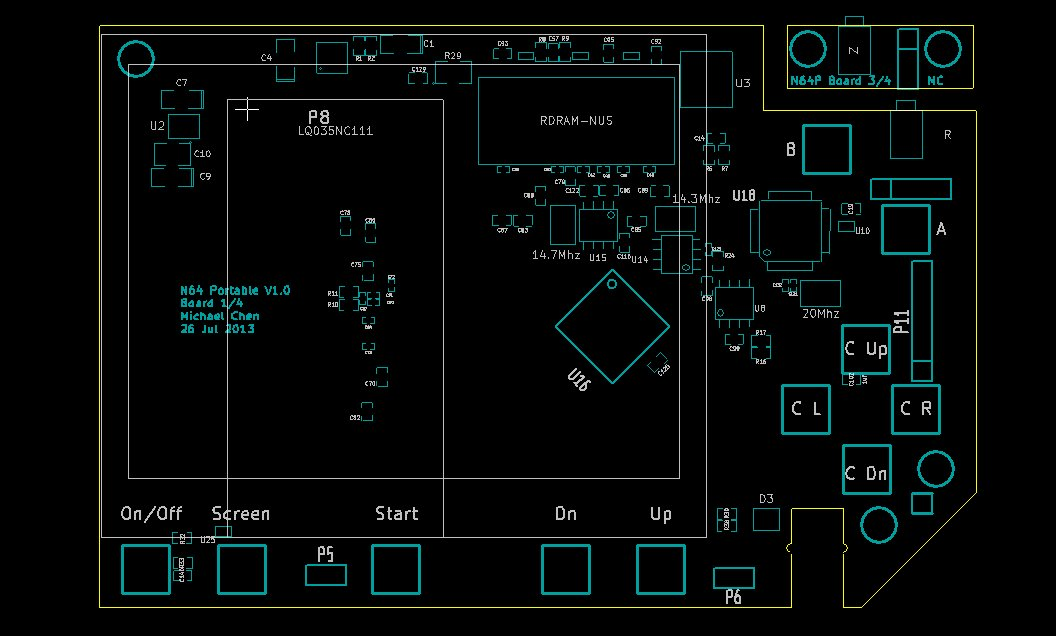
reference/PCB-Designs/layout.jpg
