dmkfasi/nus-cpu/reference/Pinouts/CNT-NUS-Pinout.png

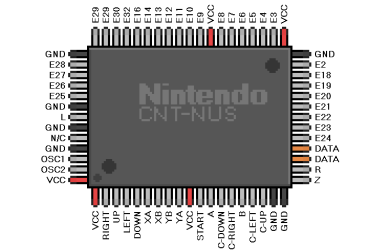
reference/Pinouts/CNT-NUS-Pinout.png
