dmkfasi/nus-cpu/reference/Schematics/N64 EAGLE schematics/observations/regulator design.GIF

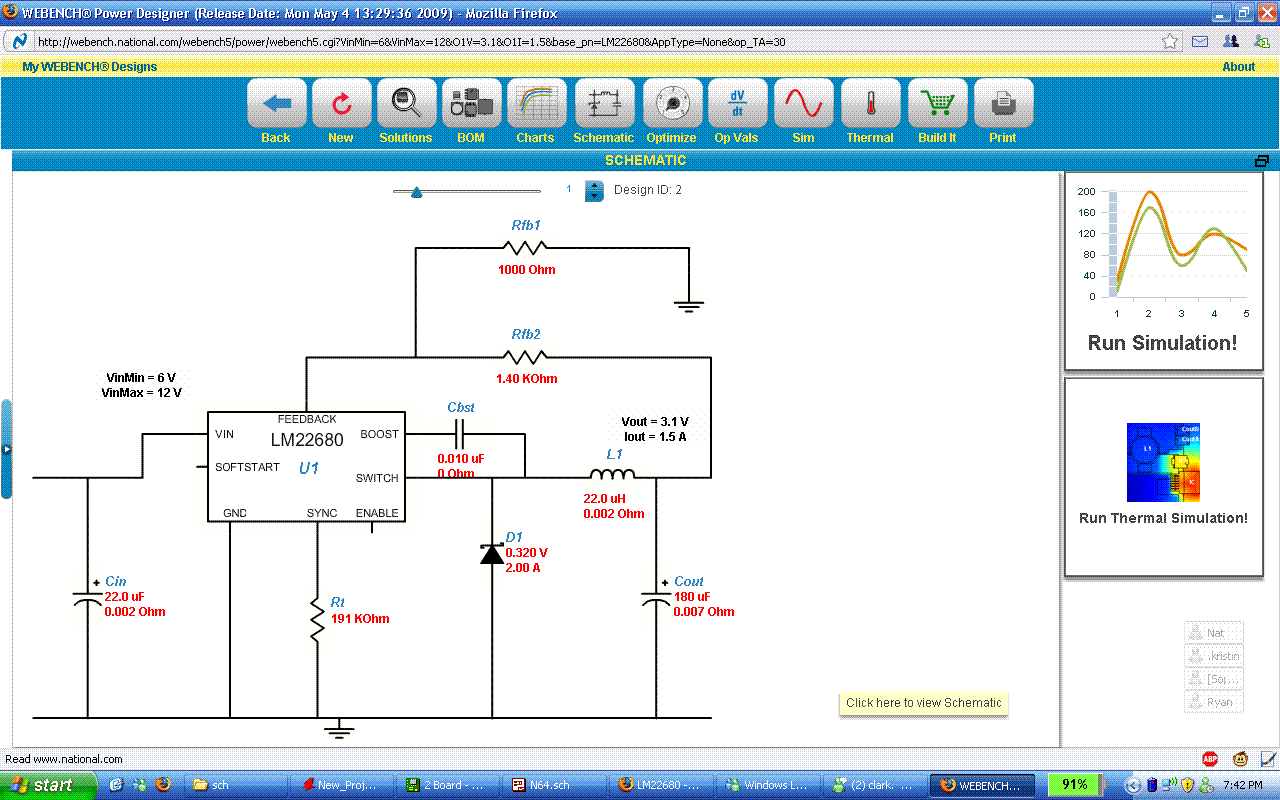
reference/Schematics/N64 EAGLE schematics/observations/regulator design.GIF
