dmkfasi/nus-cpu/reference/Schematics/N64 EAGLE schematics/observations/removed transistor.GIF

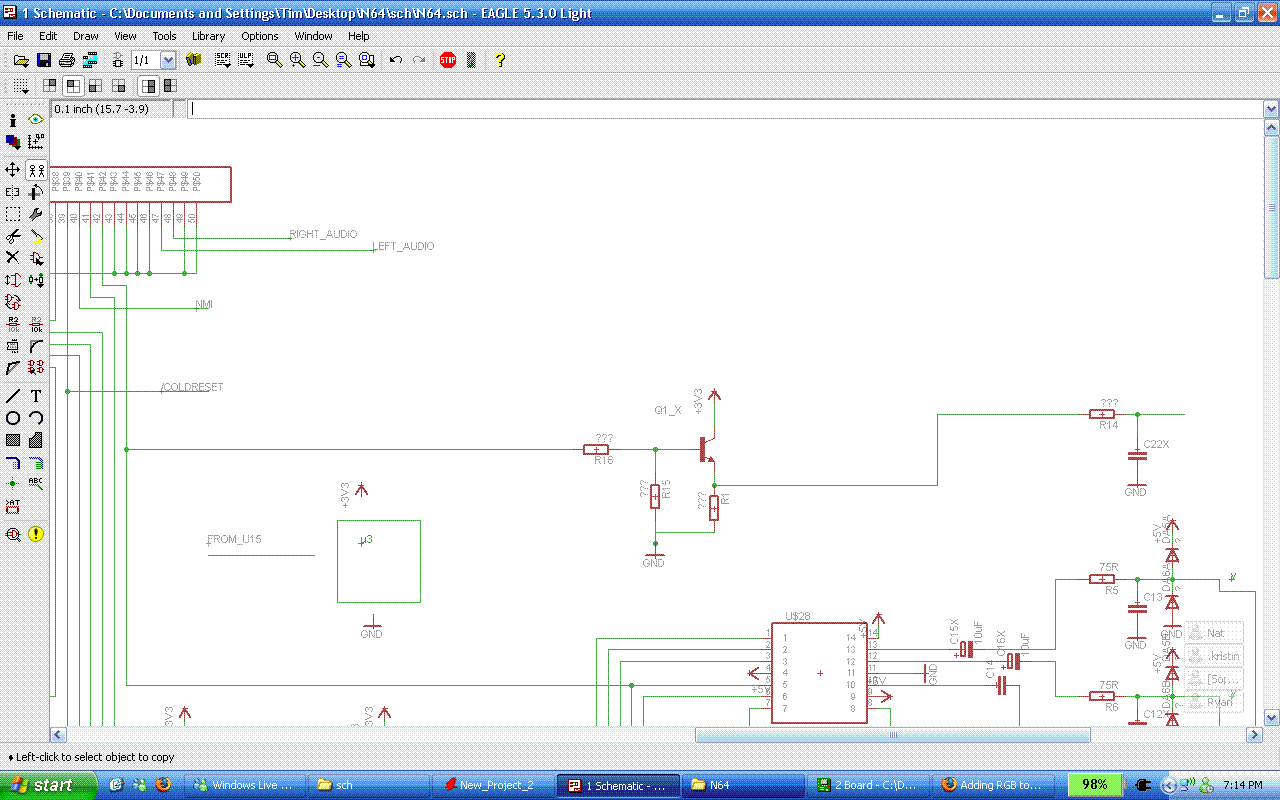
reference/Schematics/N64 EAGLE schematics/observations/removed transistor.GIF
