dmkfasi/nus-cpu/reference/Pinouts/CPU-RCP-Slot-PIF-wiring.png

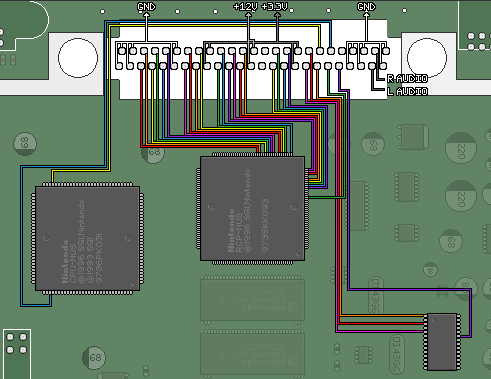
reference/Pinouts/CPU-RCP-Slot-PIF-wiring.png
